inertialsense/IS-hdw/Products/IK-1/IK-1-2/README.md

# IK-1

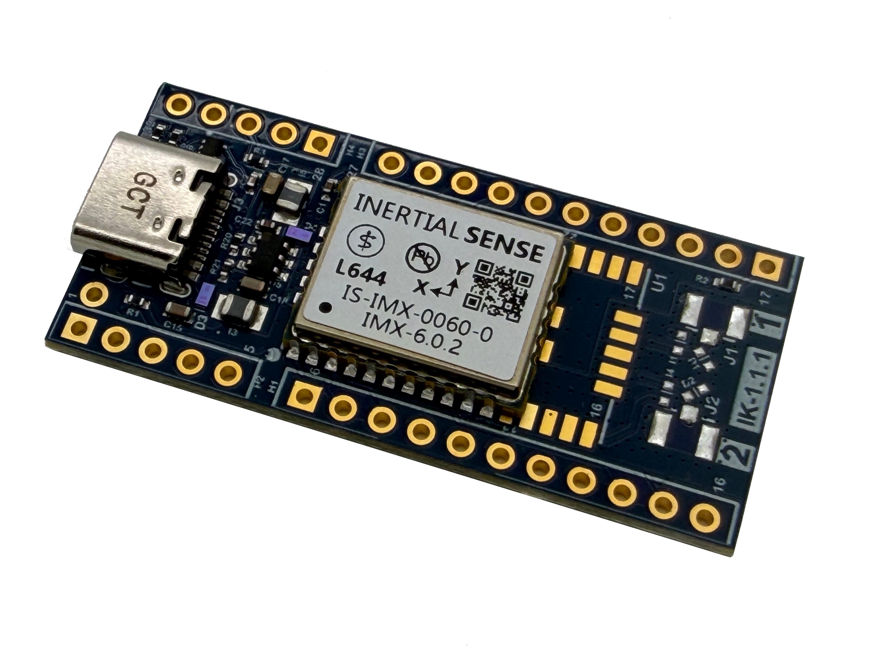
[picture p15: Products/IK-1/IK-1-2/Images/ik-1.png]
IK-1


The InertialSense IK-1 is a breakout board usable with the IMX or GPX dual multi-band GNSS receiver, exposing all pins for evaluation and development.  The IK-1 headers are 0.1" pitch.

## LICENSE



Use these Hardware Design files as you wish.  Inertial Sense is not liable for any claim, damages, or other liability resulting from their use.  See the included *LICENSE* file for details.

------

## Support

Email - support@inertialsense.com

------

(c) 2014-2026 Inertial Sense, Inc.
