inertialsense/IS-hdw/Products/EVB-1/EVB-1-5/Images/evb-1.5.png

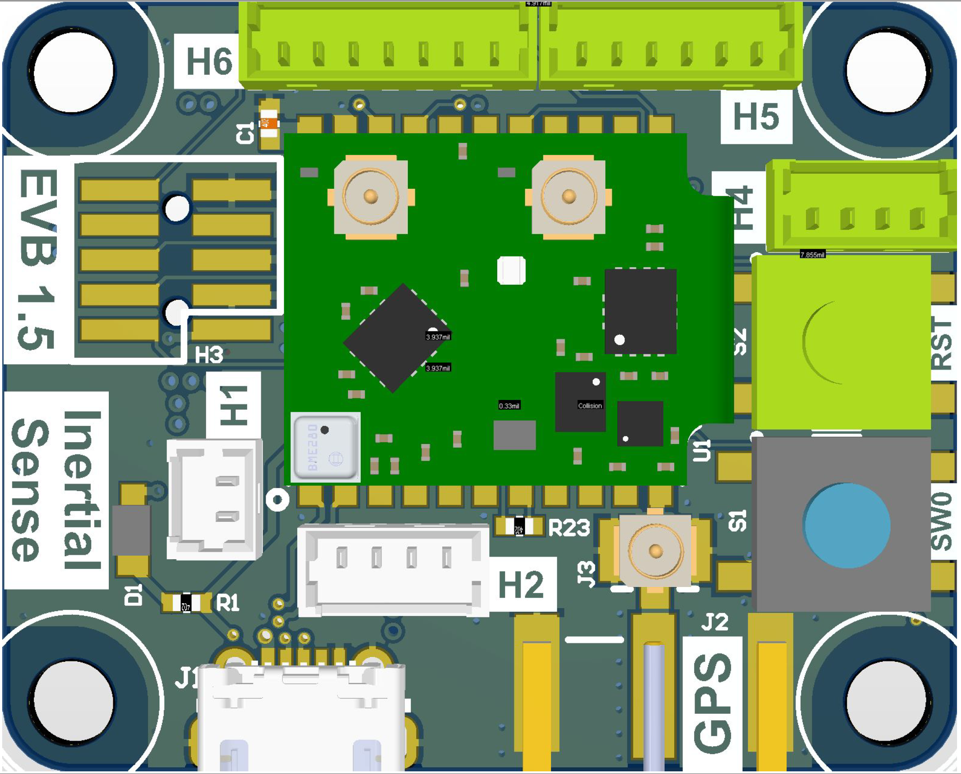
Products/EVB-1/EVB-1-5/Images/evb-1.5.png
