inertialsense/IS-hdw/Products/EVB-2/EVB-2-1/Images/bottom.png

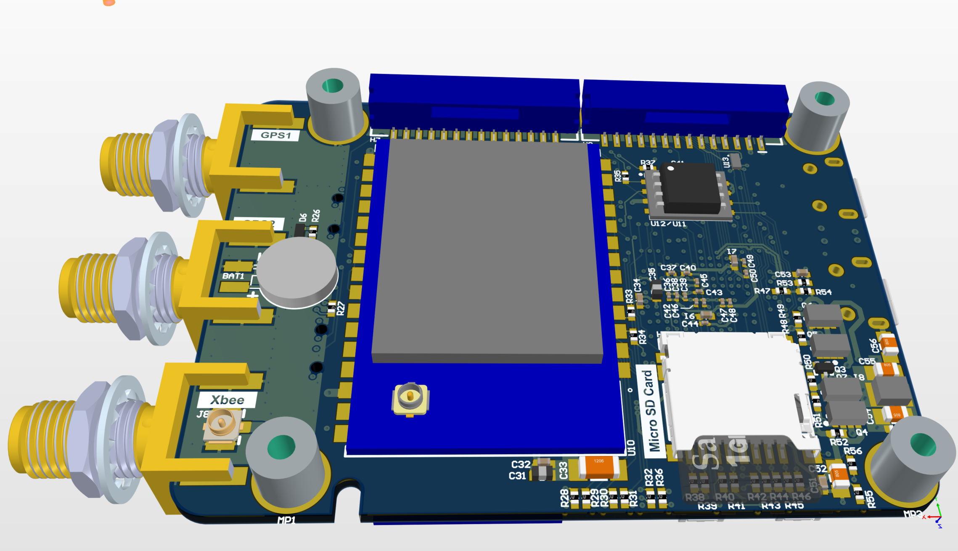
Products/EVB-2/EVB-2-1/Images/bottom.png
