inertialsense/IS-hdw/Products/EVB-2/EVB-2-1/Images/evb-2.1.2.png

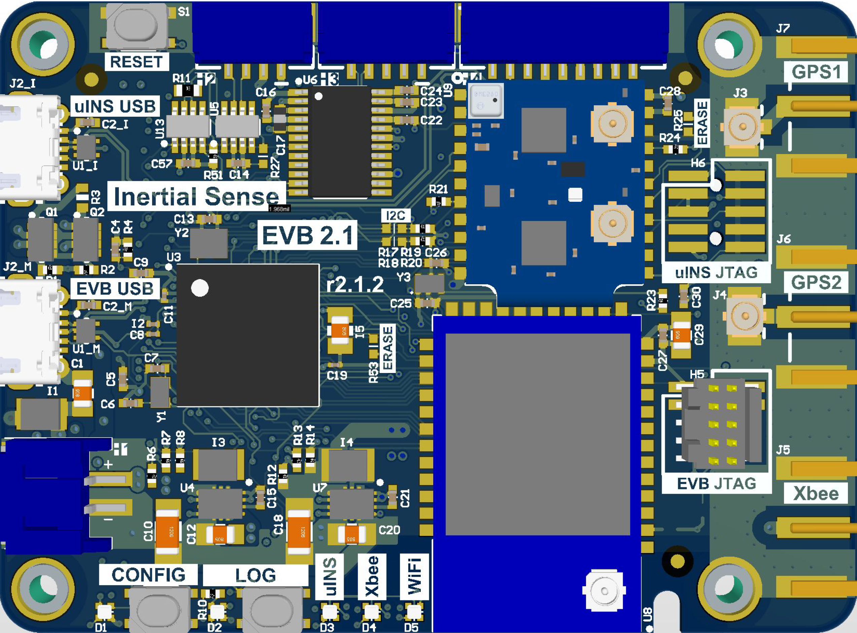
Products/EVB-2/EVB-2-1/Images/evb-2.1.2.png
