inertialsense/IS-hdw/Products/EVB-2/EVB-2-1/Images/iso-sd.jpg

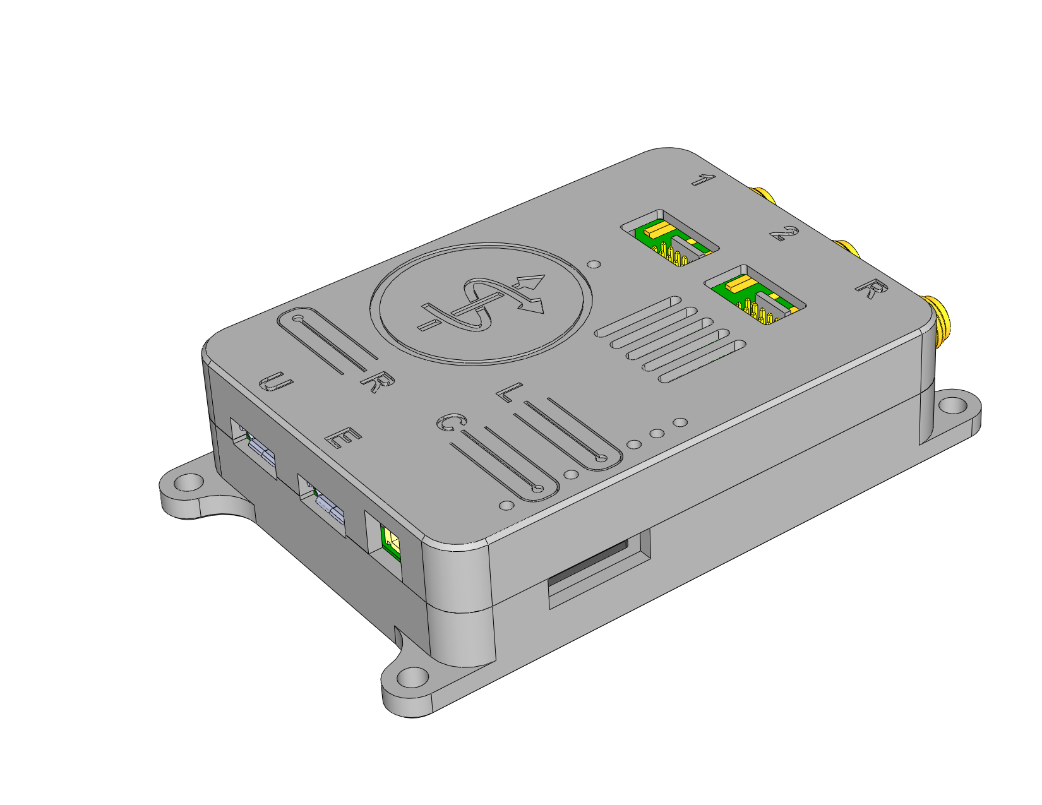
Products/EVB-2/EVB-2-1/Images/iso-sd.jpg
