inertialsense/IS-hdw/Products/GPX-1/GPX-1-0/Images/GPX_1.0.1_top.png

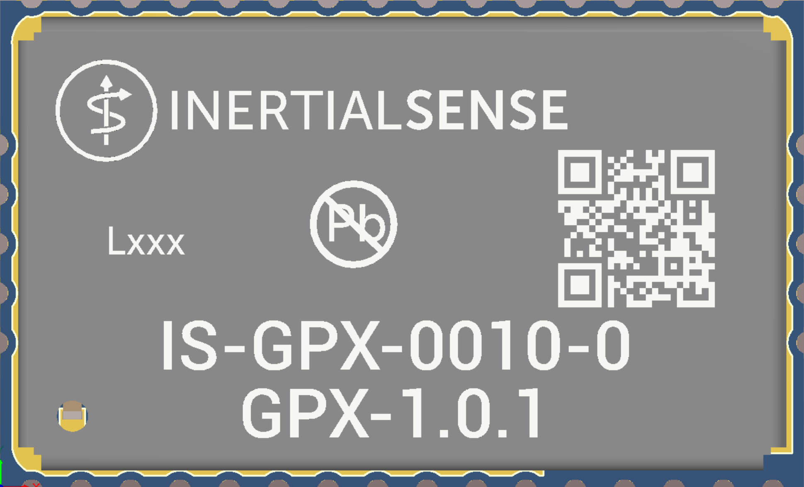
Products/GPX-1/GPX-1-0/Images/GPX_1.0.1_top.png
