inertialsense/IS-hdw/Products/IG-1/IG-1-2-G2/3D_Model/IG-1.2-G2.png

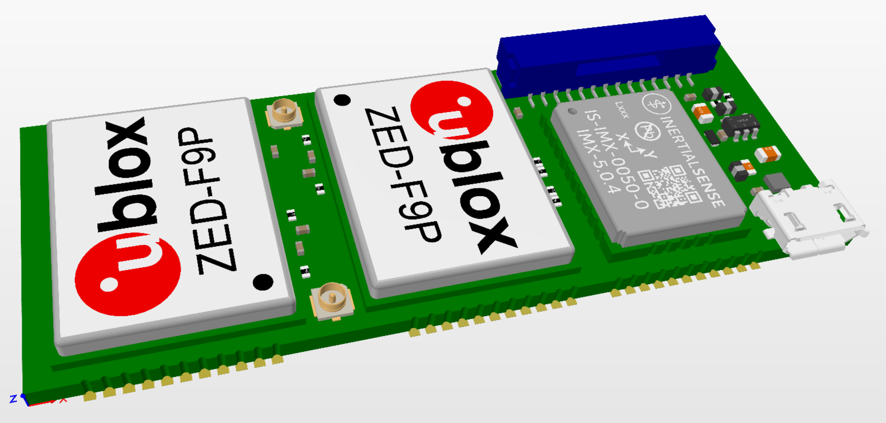
Products/IG-1/IG-1-2-G2/3D_Model/IG-1.2-G2.png
