inertialsense/IS-hdw/Products/IG-1/IG-1-2-G2/Images/IG-1.1_iso.png

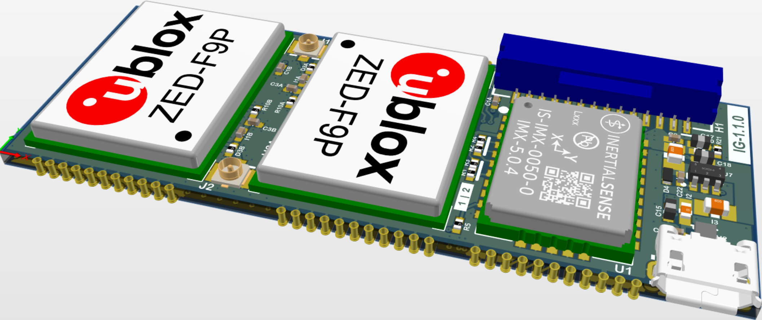
Products/IG-1/IG-1-2-G2/Images/IG-1.1_iso.png
