inertialsense/IS-hdw/Products/IG-3/IG-3-0-G/3D_Model/ig-2.1_1000w.png

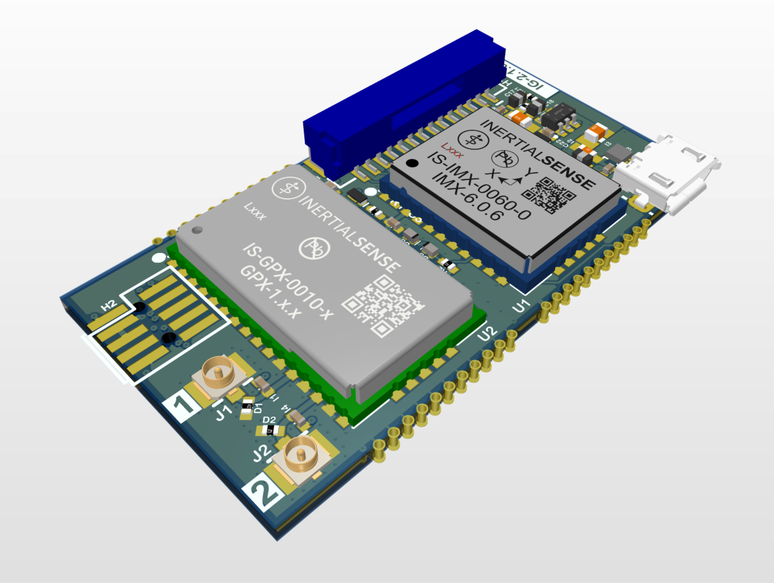
Products/IG-3/IG-3-0-G/3D_Model/ig-2.1_1000w.png
