inertialsense/IS-hdw/Products/IK-1/IK-1-1/Images/ik-1_cad.png

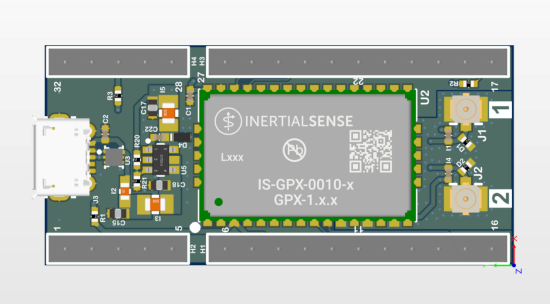
Products/IK-1/IK-1-1/Images/ik-1_cad.png
