inertialsense/IS-hdw/Products/IK-1/IK-1-2/Images/ik-1-gpx_cad.png

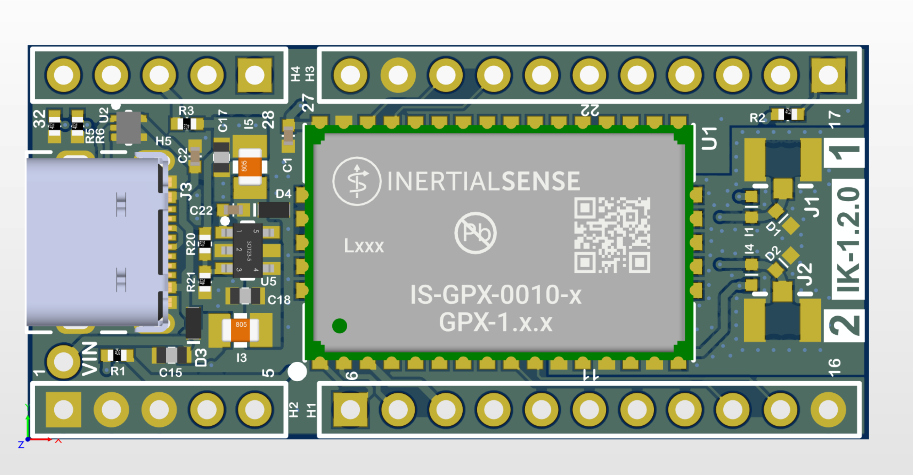
Products/IK-1/IK-1-2/Images/ik-1-gpx_cad.png
