inertialsense/IS-hdw/Products/IMX-5/IMX-5-0/3D_Model/IMX-5.0.4_top.png

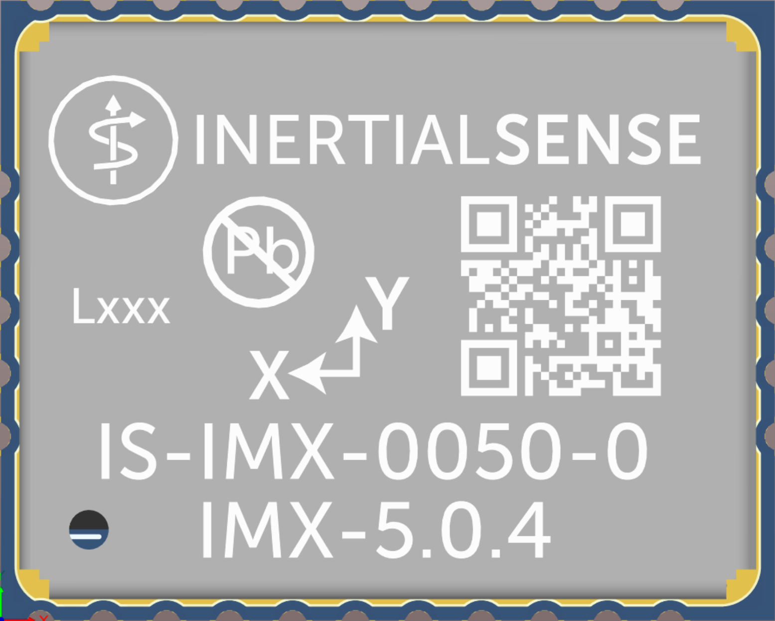
Products/IMX-5/IMX-5-0/3D_Model/IMX-5.0.4_top.png
