inertialsense/IS-hdw/Products/RUG-1/RUG-1-1/Images/rugged05x-600x400.png

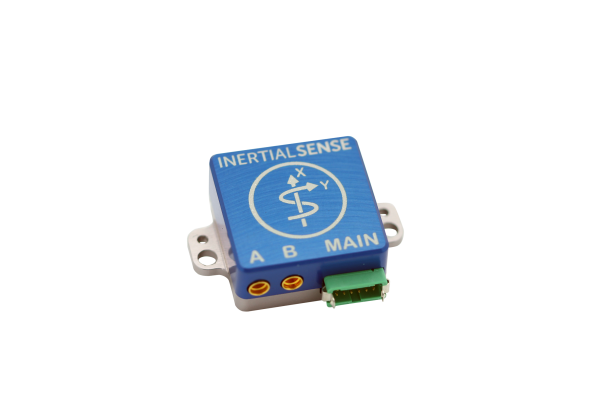
Products/RUG-1/RUG-1-1/Images/rugged05x-600x400.png
