inertialsense/IS-hdw/Products/RUG-1/RUG-1-1/Images/rugged 1 45d large.jpg

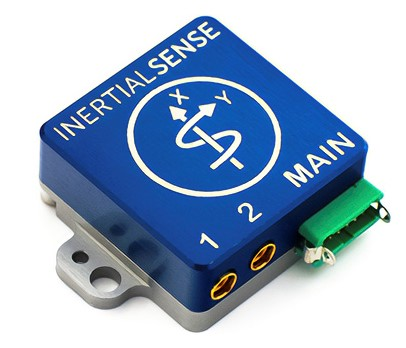
Products/RUG-1/RUG-1-1/Images/rugged 1 45d large.jpg
