inertialsense/IS-hdw/Products/RUG-2/RUG-2-0/Images/Rugged-Dip-Switch.jpg

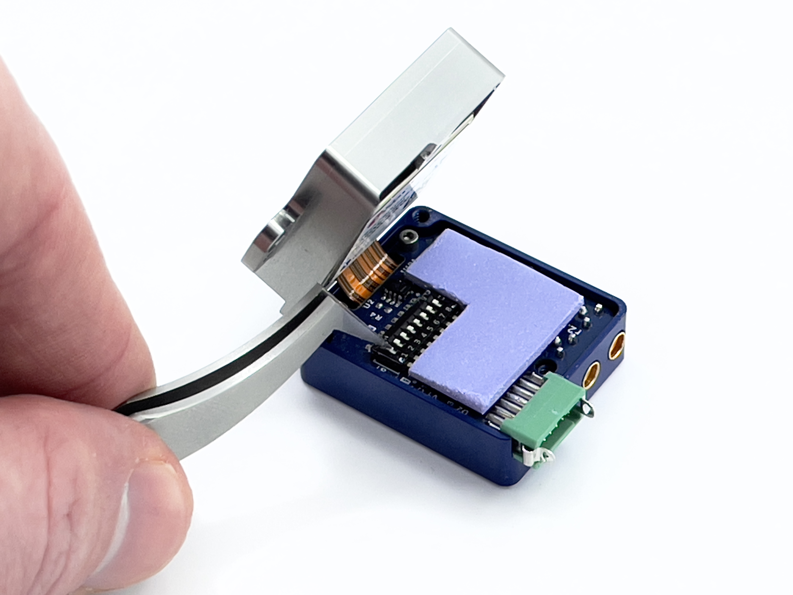
Products/RUG-2/RUG-2-0/Images/Rugged-Dip-Switch.jpg
