inertialsense/IS-hdw/Products/RUG-3/RUG-3-0-G0/Images/rug-3.0-G0_cad.png

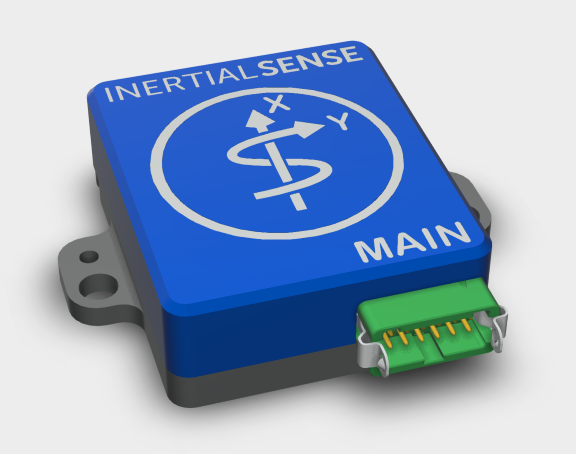
Products/RUG-3/RUG-3-0-G0/Images/rug-3.0-G0_cad.png
