inertialsense/IS-hdw/Products/EVB-2/EVB-2-1/Images/EVB-2 Case Assembly shaded con.jpg

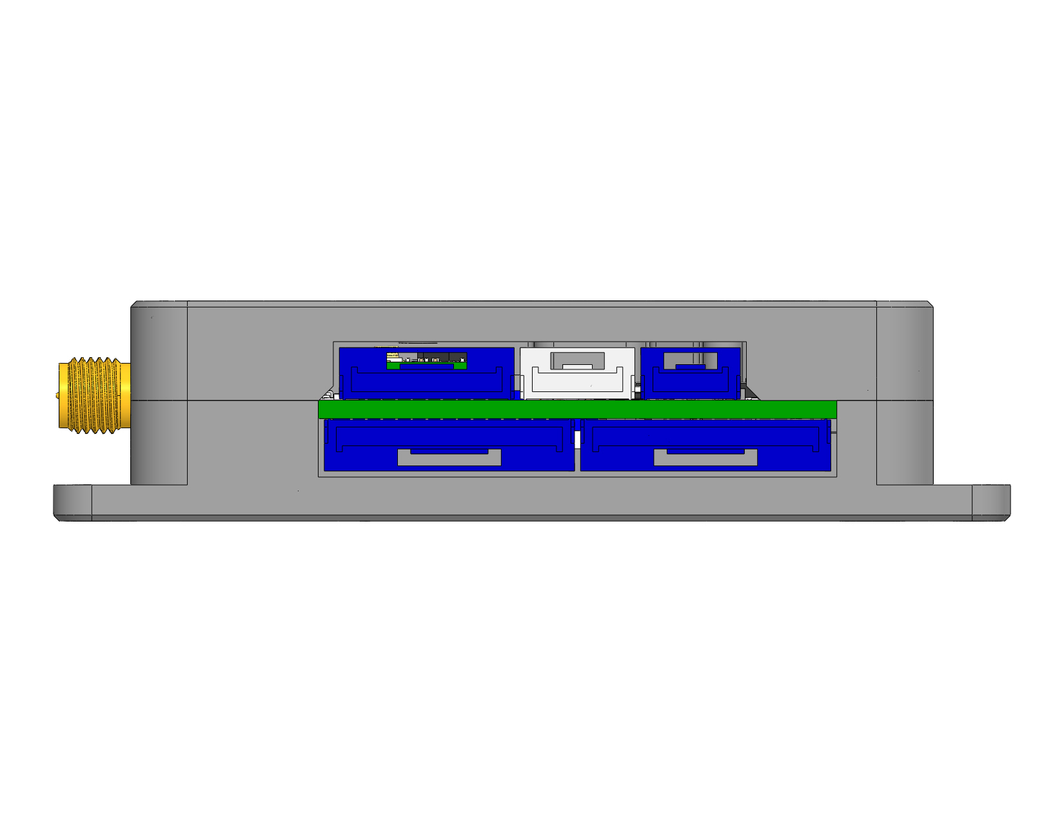
Products/EVB-2/EVB-2-1/Images/EVB-2 Case Assembly shaded con.jpg
