inertialsense/IS-hdw/Products/RUG-1/RUG-1-1/Images/comparison assembly shaded (7).jpg

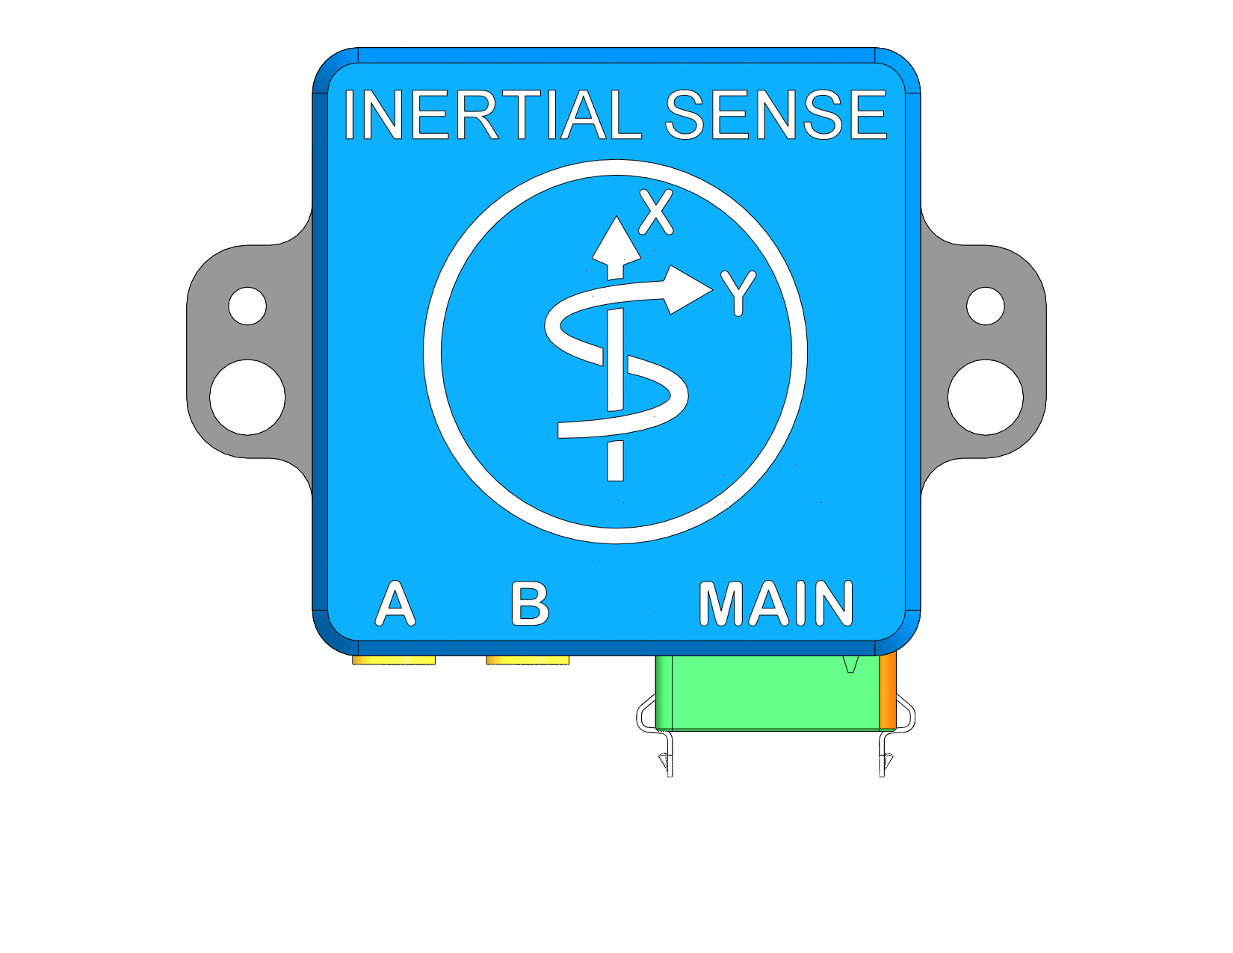
Products/RUG-1/RUG-1-1/Images/comparison assembly shaded (7).jpg
