inertialsense/IS-hdw/Products/RUG-1/RUG-1-1/Images/Ruggedized uINS Assembly shaded.jpg

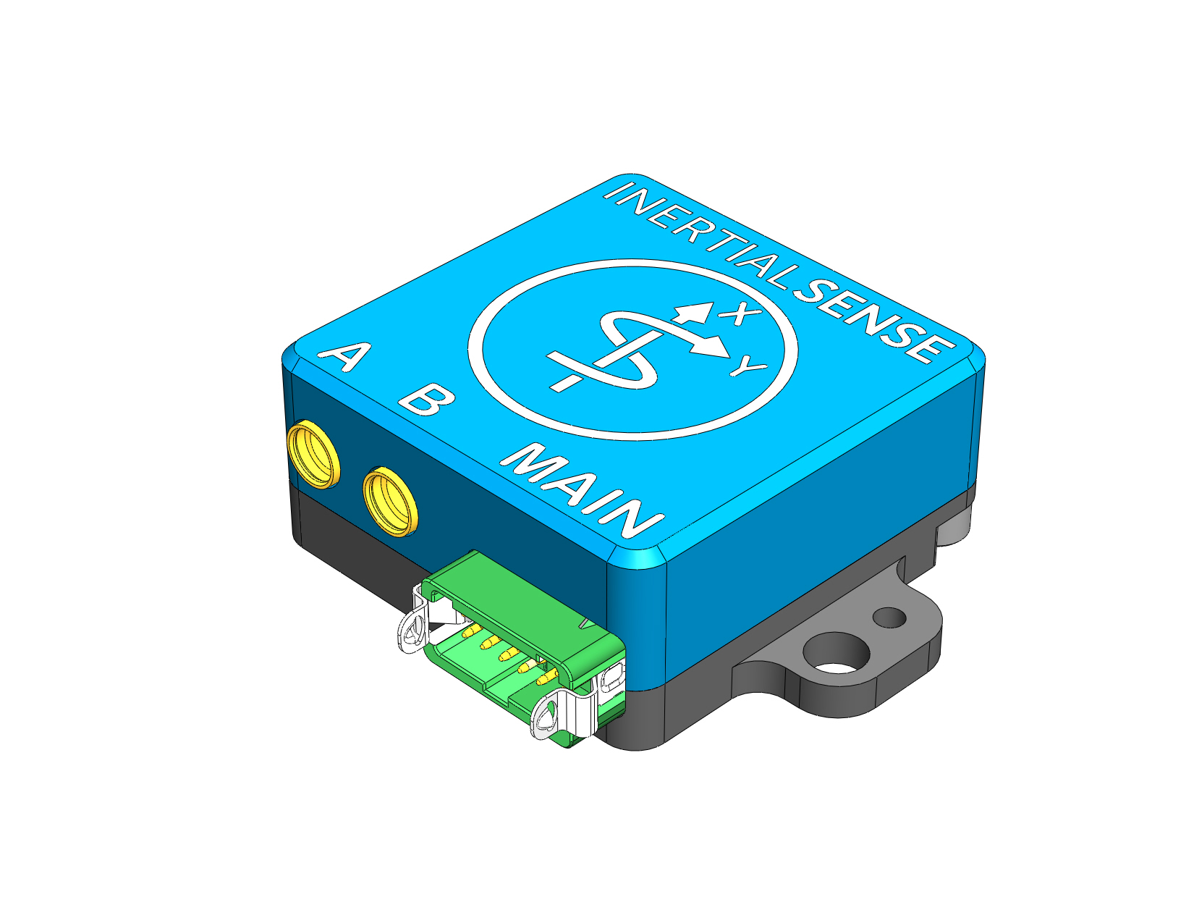
Products/RUG-1/RUG-1-1/Images/Ruggedized uINS Assembly shaded.jpg
