inertialsense/IS-hdw/Products/IG-2/IG-2-0/Schematic/IG-2_schematic.PDF

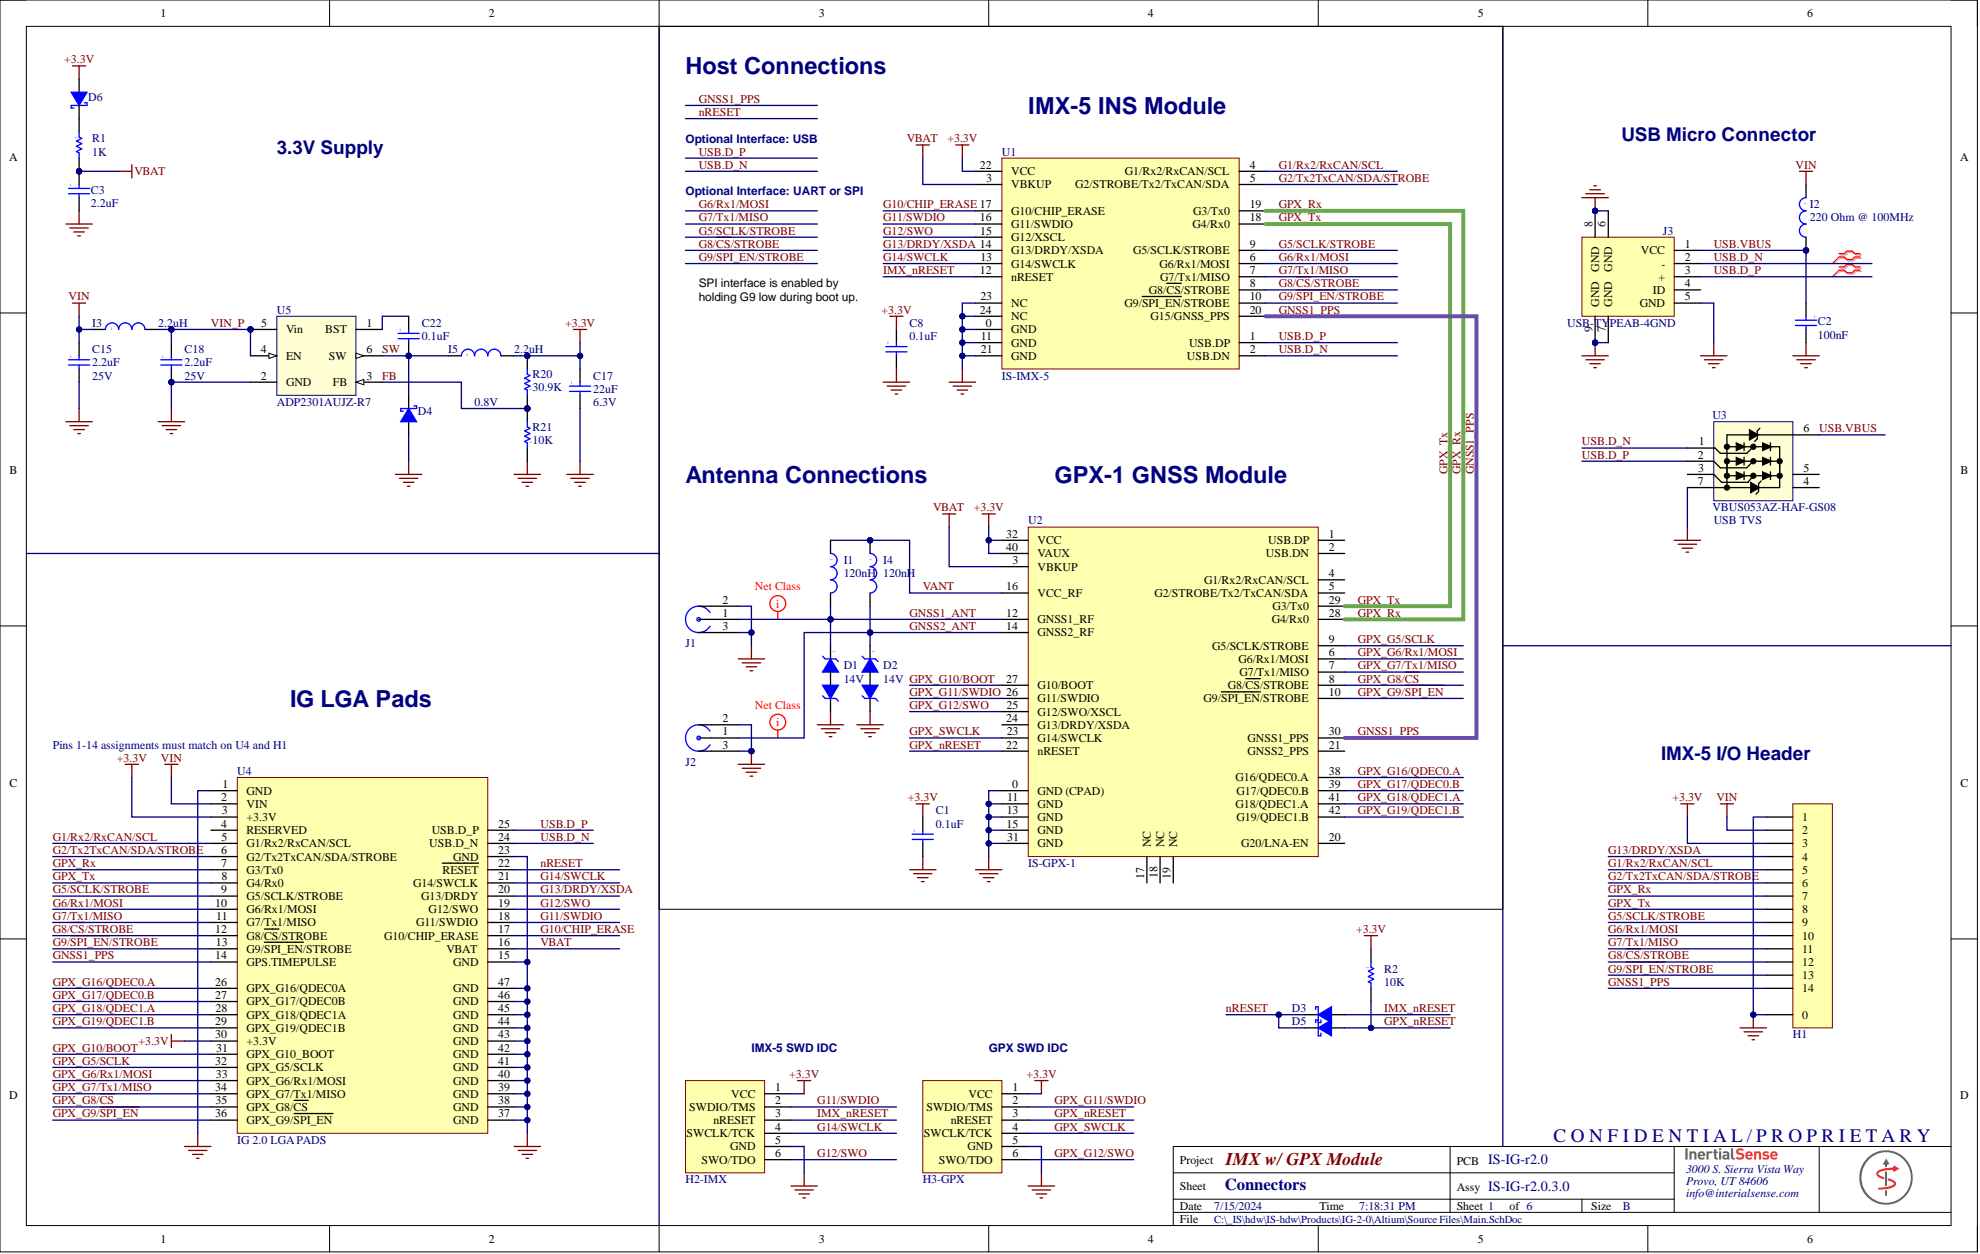
[picture p77: page 1]

G6/Rx1/MOSI G5/SCLK/STROBE G8/CS/STROBE G2/Tx2TxCAN/SDA/STROBE G1/Rx2/RxCAN/SCL

Optional Interface: UART or SPI
G5/SCLK/STROBE G8/CS/STROBE G9/SPI_EN/STROBE G6/Rx1/MOSI G7/Tx1/MISO

SPI interface is enabled by
holding G9 low during boot up.

1 1
GND 21

GPX_G6/Rx1/MOSI GPX_G7/Tx1/MISO GPX_G5/SCLK GPX_G8/CS GPX_G9/SPI_EN

Pins 1-14 assignments must match on U4 and H1

G6/Rx1/MOSI G5/SCLK/STROBE G8/CS/STROBE G2/Tx2TxCAN/SDA/STROBE G1/Rx2/RxCAN/SCL G9/SPI_EN/STROBE G7/Tx1/MISO GNSS1_PPS

G13/DRDY/XSDA

GPX_G10/BOOT
