inertialsense/IS-hdw/Products/EVB-2/EVB-2-1/Schematic/EVB-2-1-2_Schematic Prints.PDF

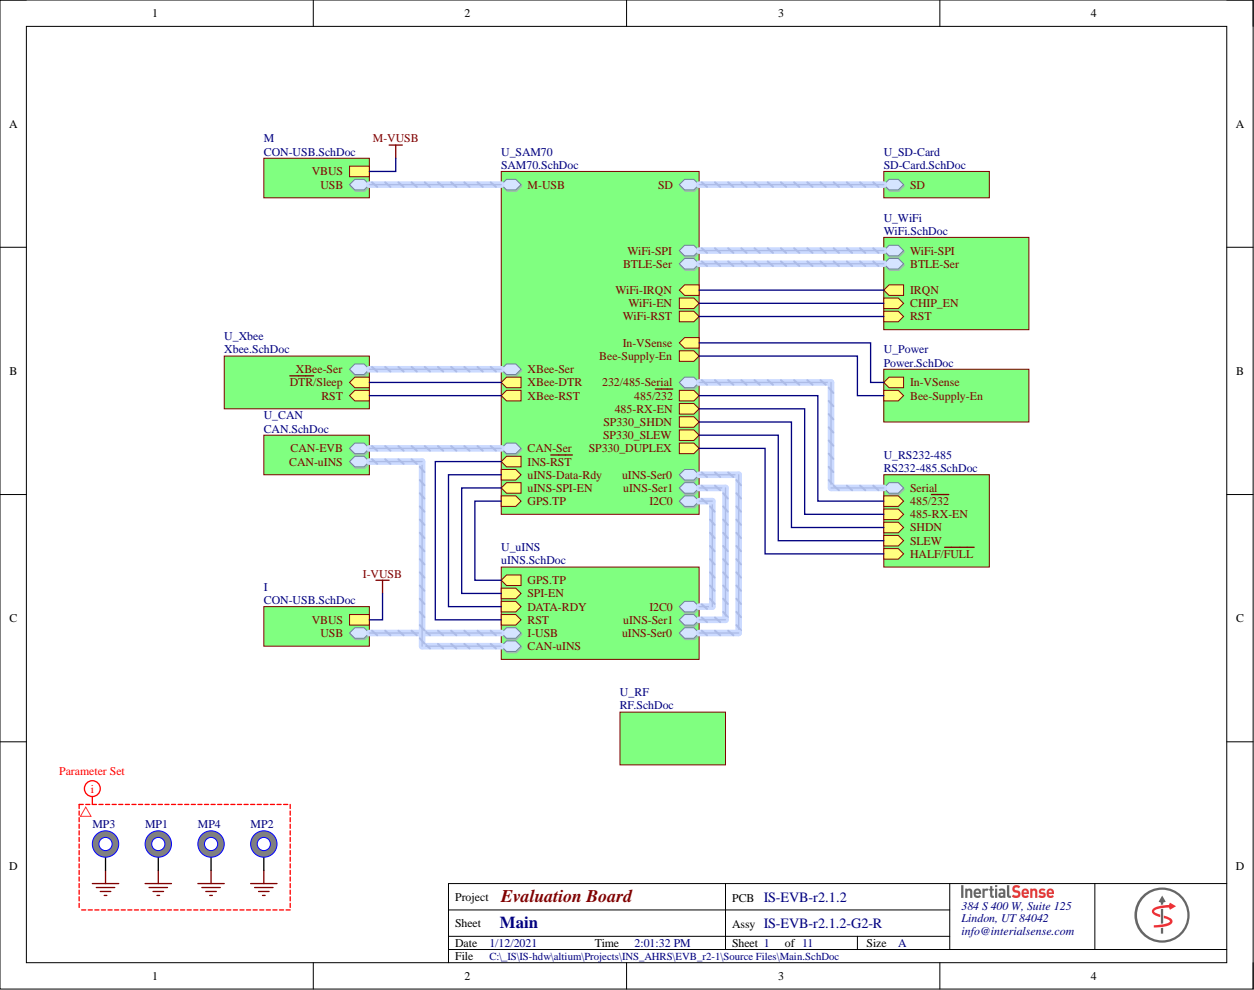
[picture p78: page 1]

U_SD-Card SD-Card.SchDoc

WiFi-IRQN WiFi-EN WiFi-RST

U_Power
Power.SchDoc
Bee-Supply-En In-VSense

IS-EVB-r2.1.2
PCB
IS-EVB-r2.1.2-
Assy
urce Files\Main.SchDo

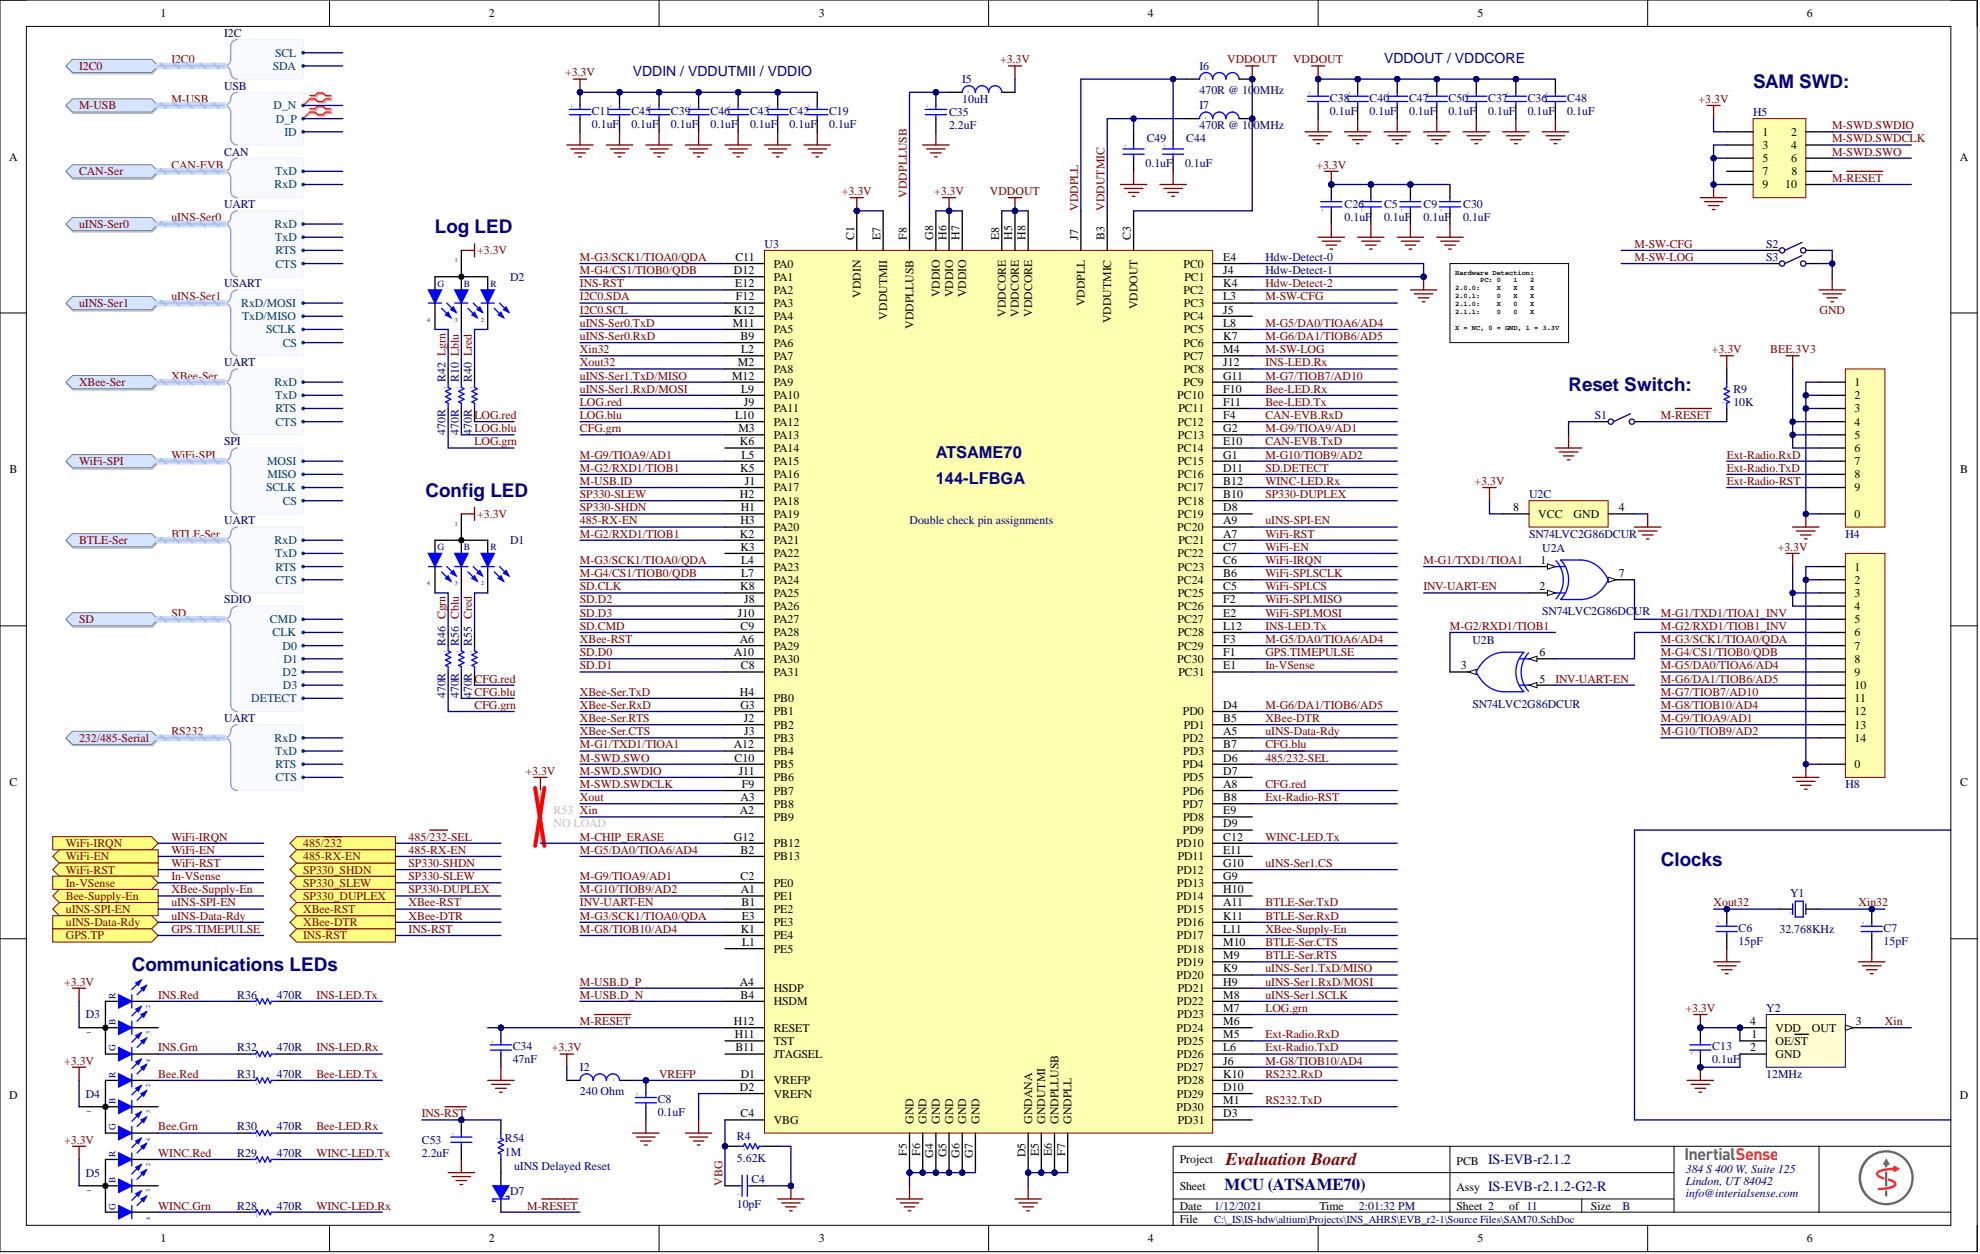
[picture p79: page 2]

GND F6 GND F5 Double check pin assignments

WiFi-RST
uINS-SPI-EN

C:\_IS\IS-hdw\altium\Projects\INS_AHRS\EVB_r2-1\Source Files\SAM70.SchDoc

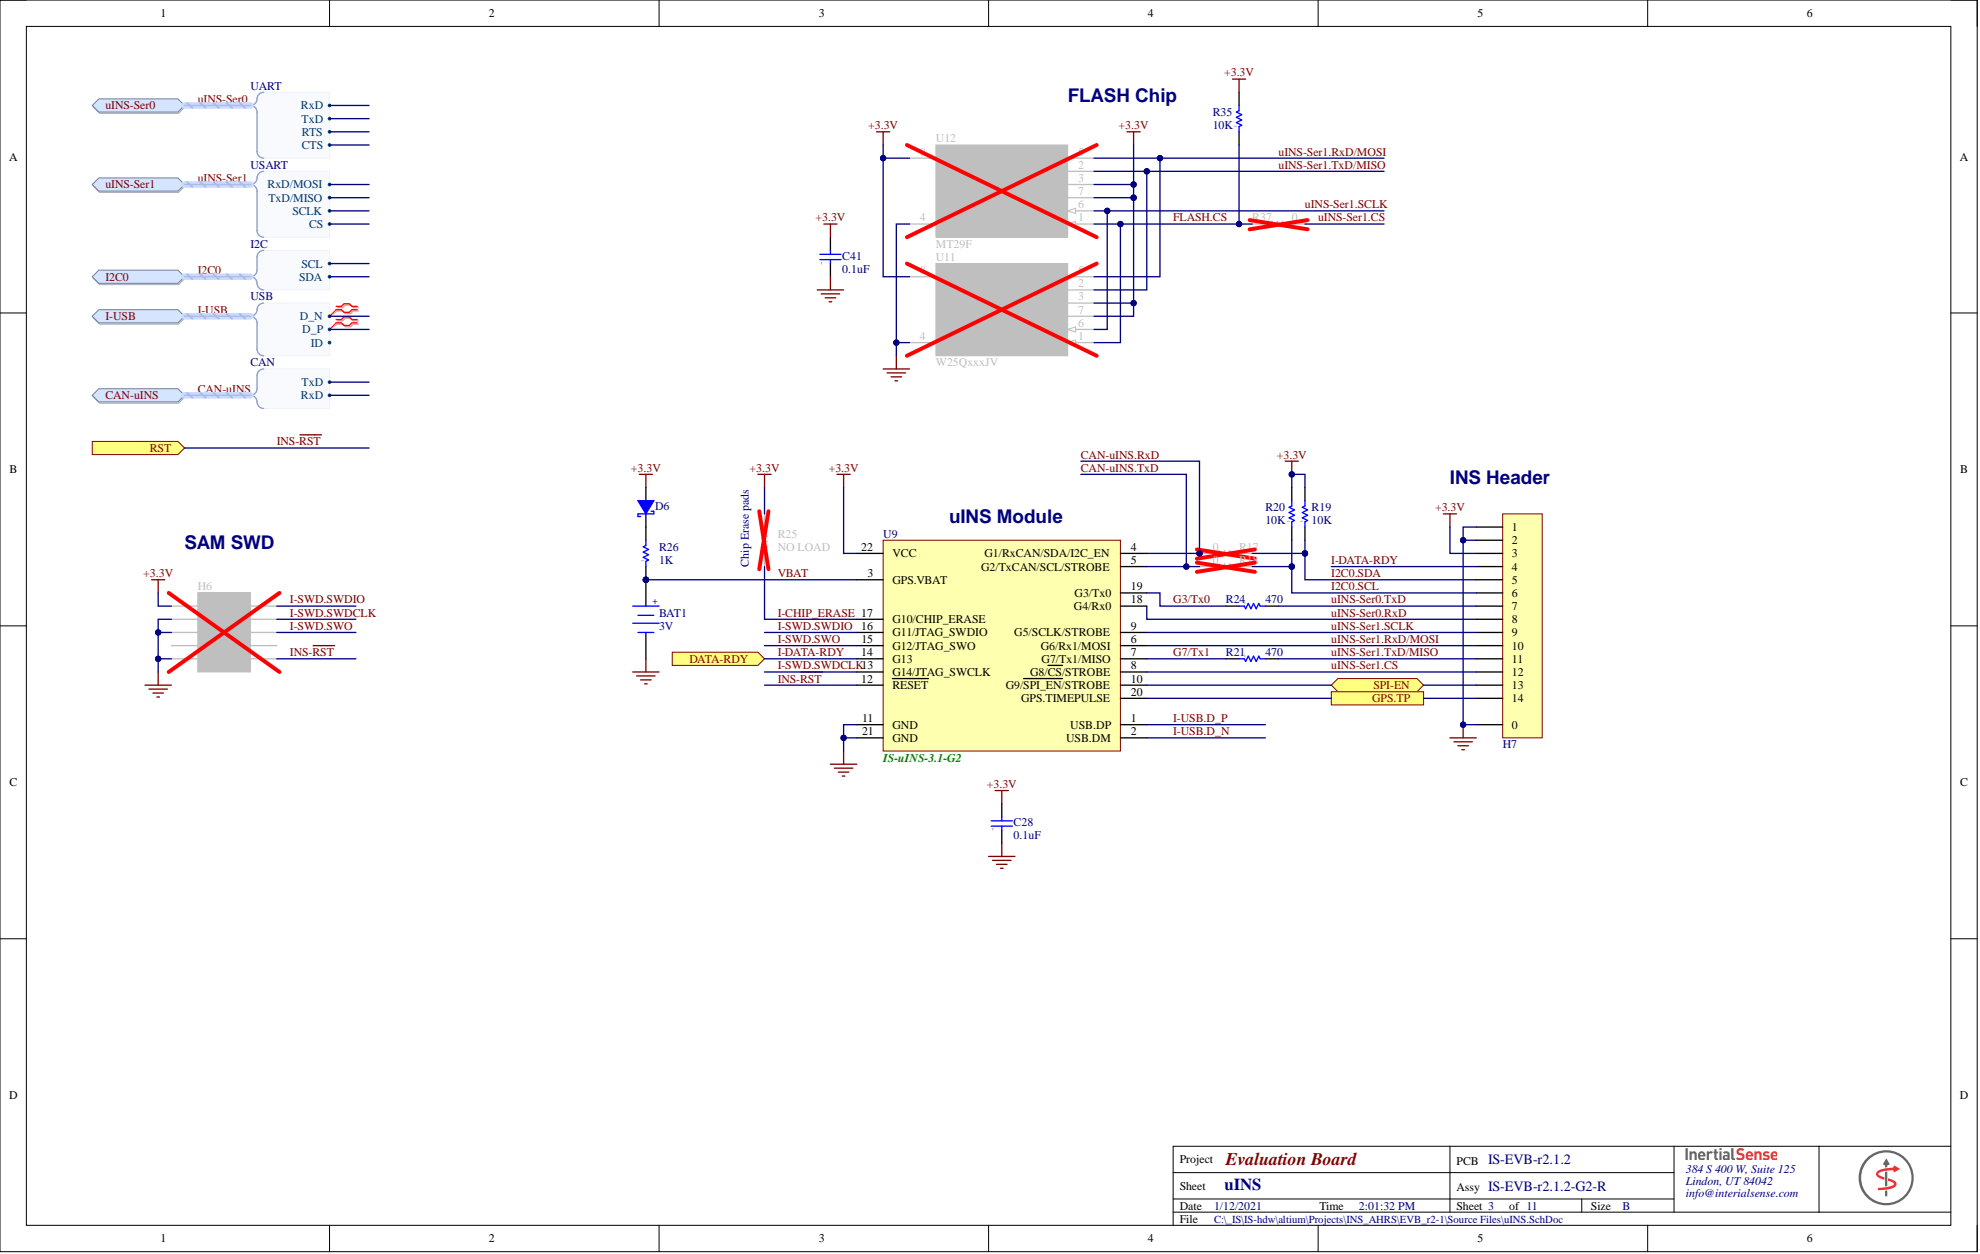
[picture p80: page 3]

C:\_IS\IS-hdw\altium\Projects\INS_AHRS\EVB_r2-1\Source Files\uINS.SchDoc

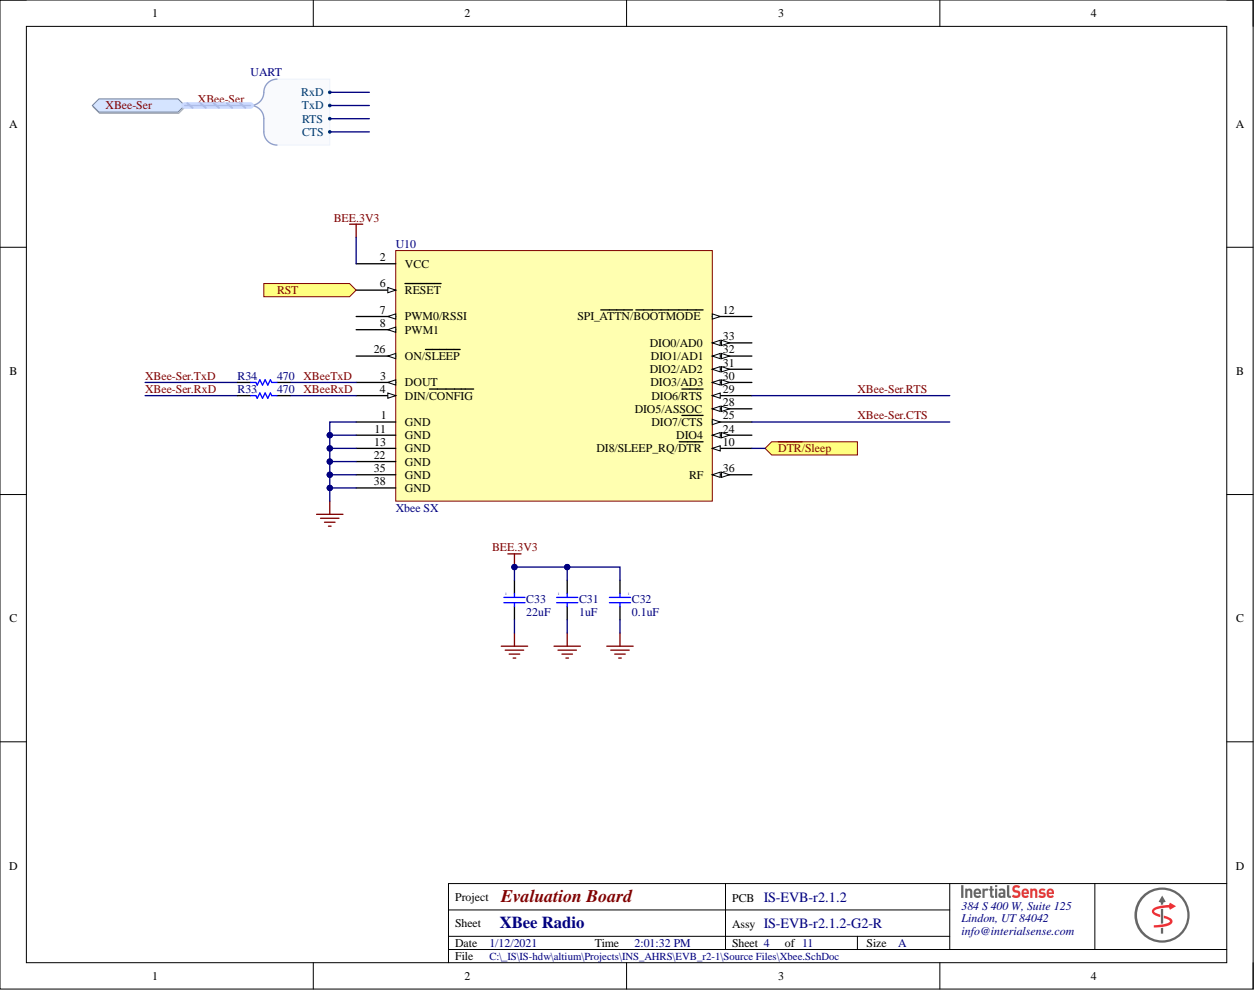
[picture p81: page 4]

C:\_IS\IS-hdw\altium\Projects\INS_AHRS\EVB_r2-1\Source Files\Xbee.SchDoc

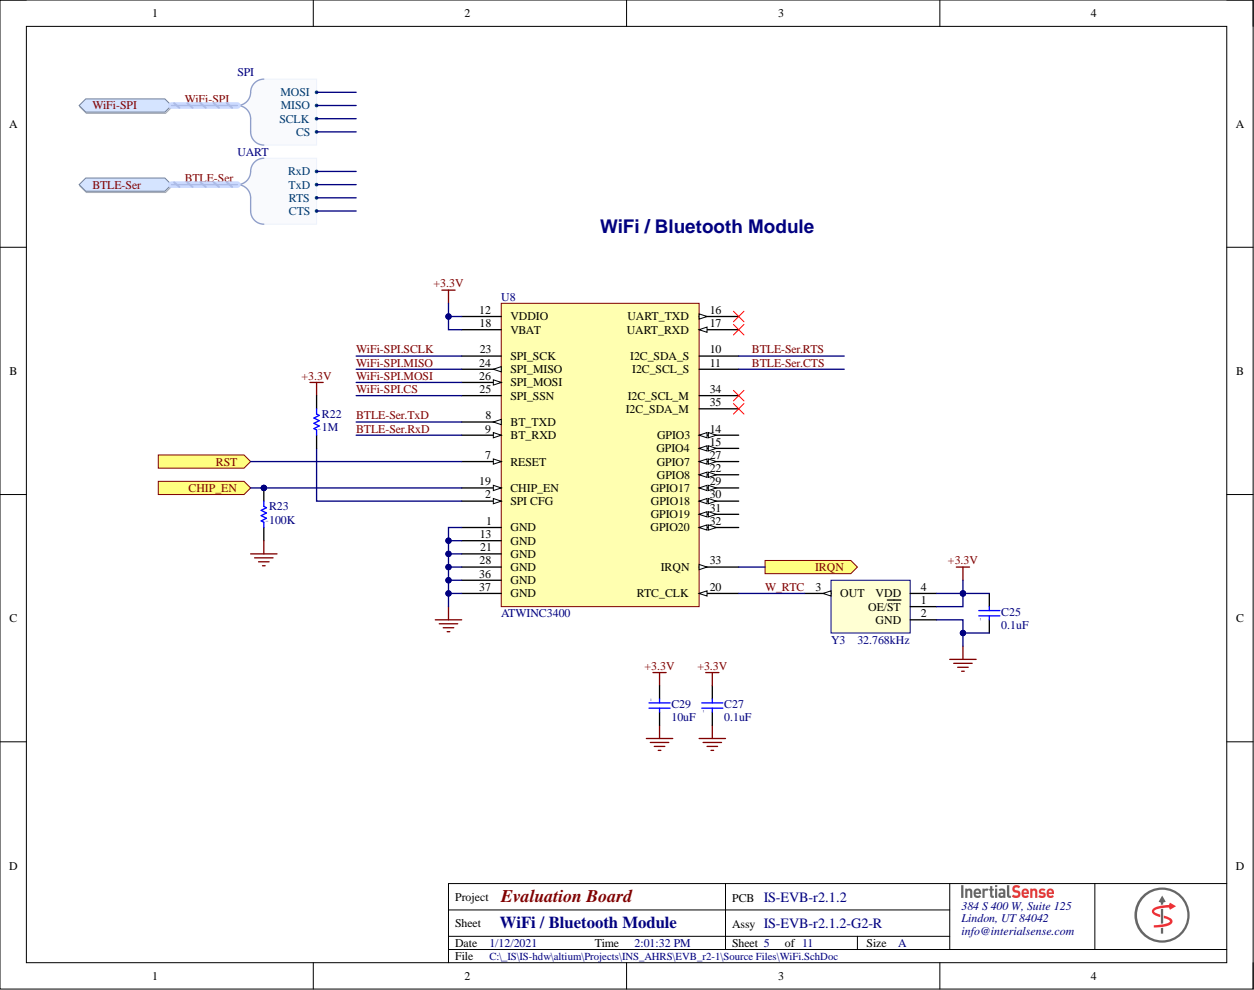
[picture p82: page 5]

C:\_IS\IS-hdw\altium\Projects\INS_AHRS\EVB_r2-1\Source Files\WiFi.SchDoc

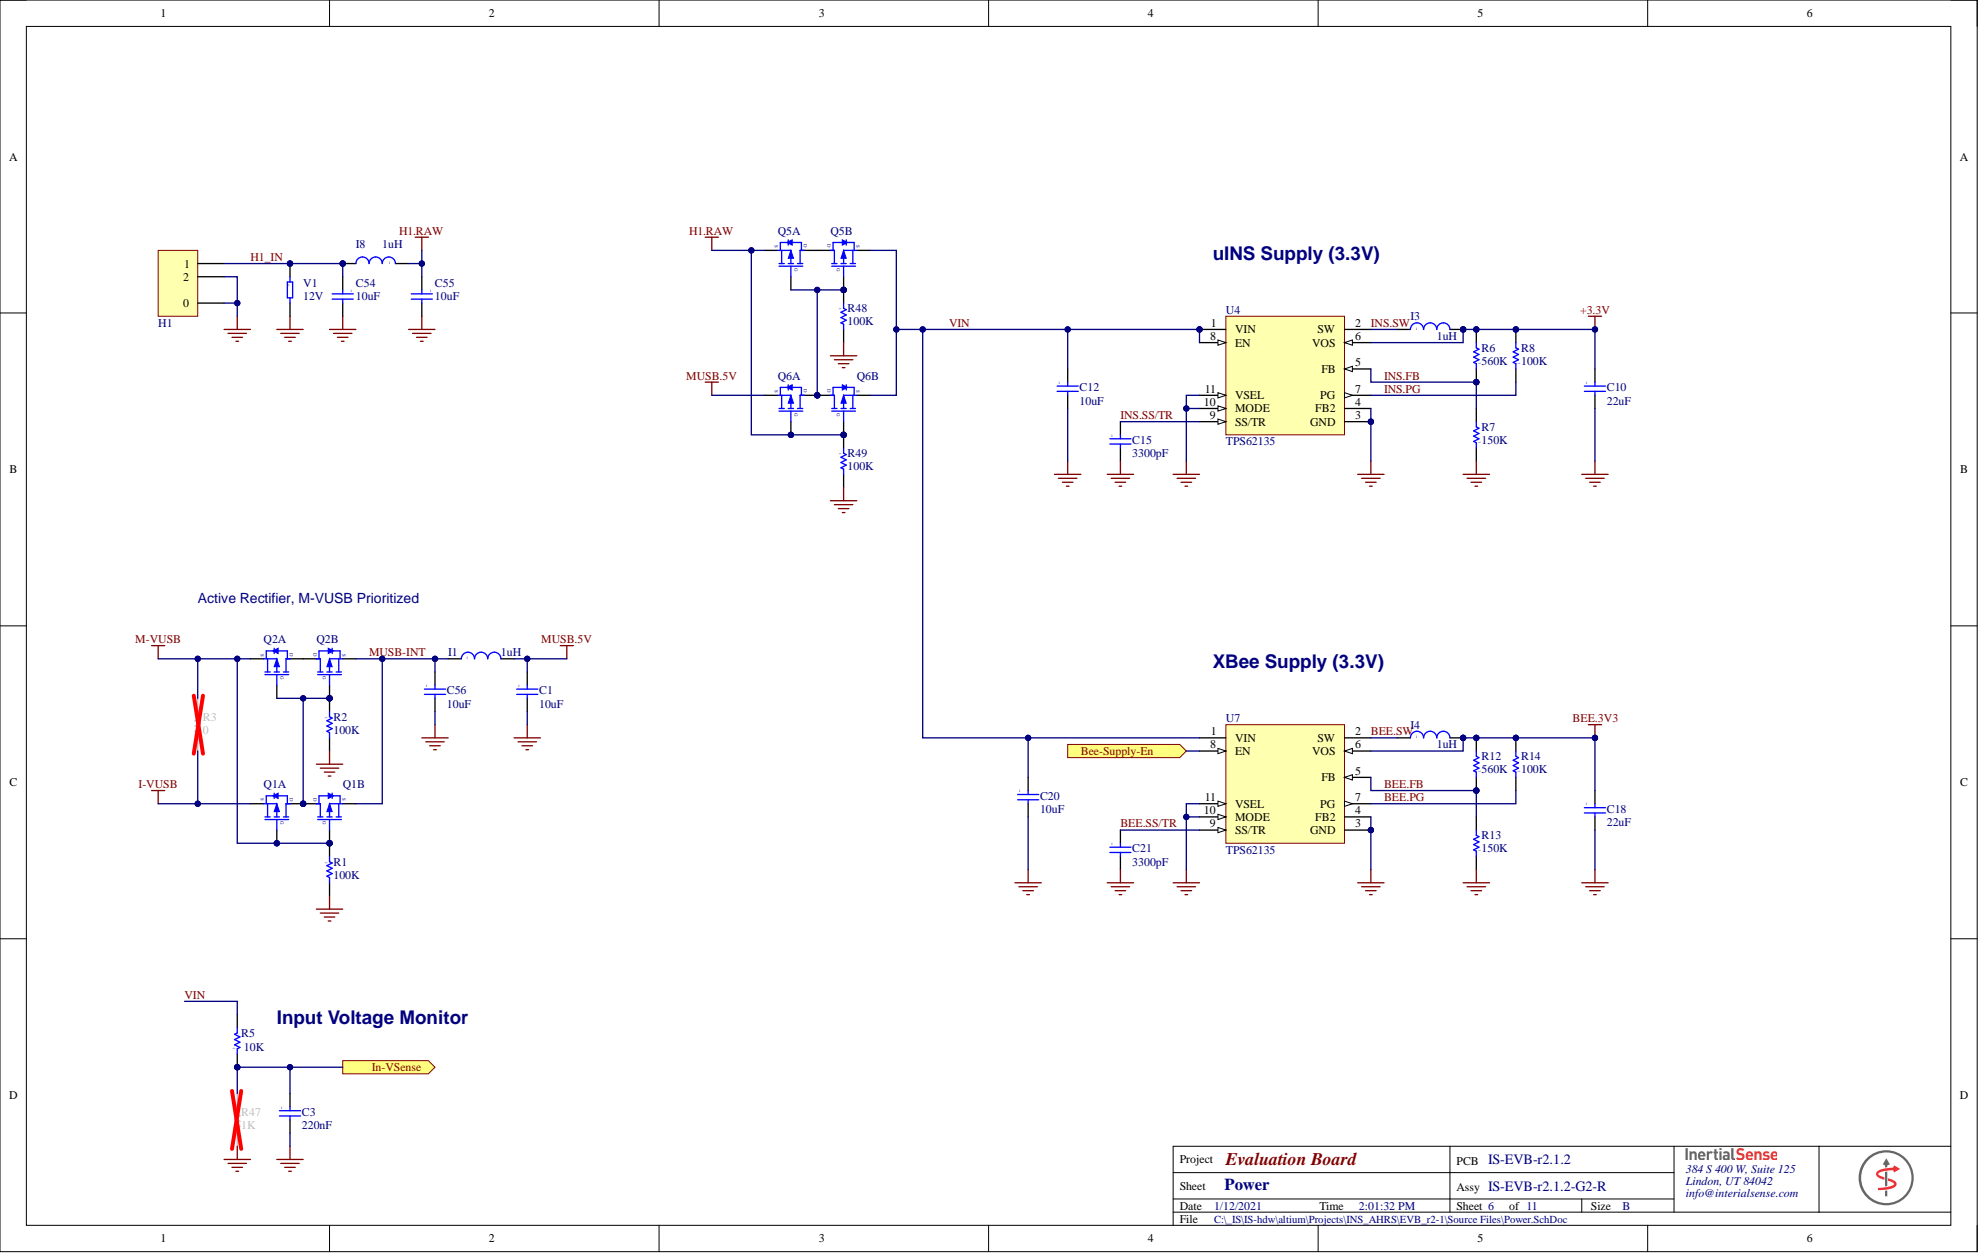
[picture p83: page 6]

Active Rectifier, M-VUSB Prioritized 10

urce Files\Power.SchDo

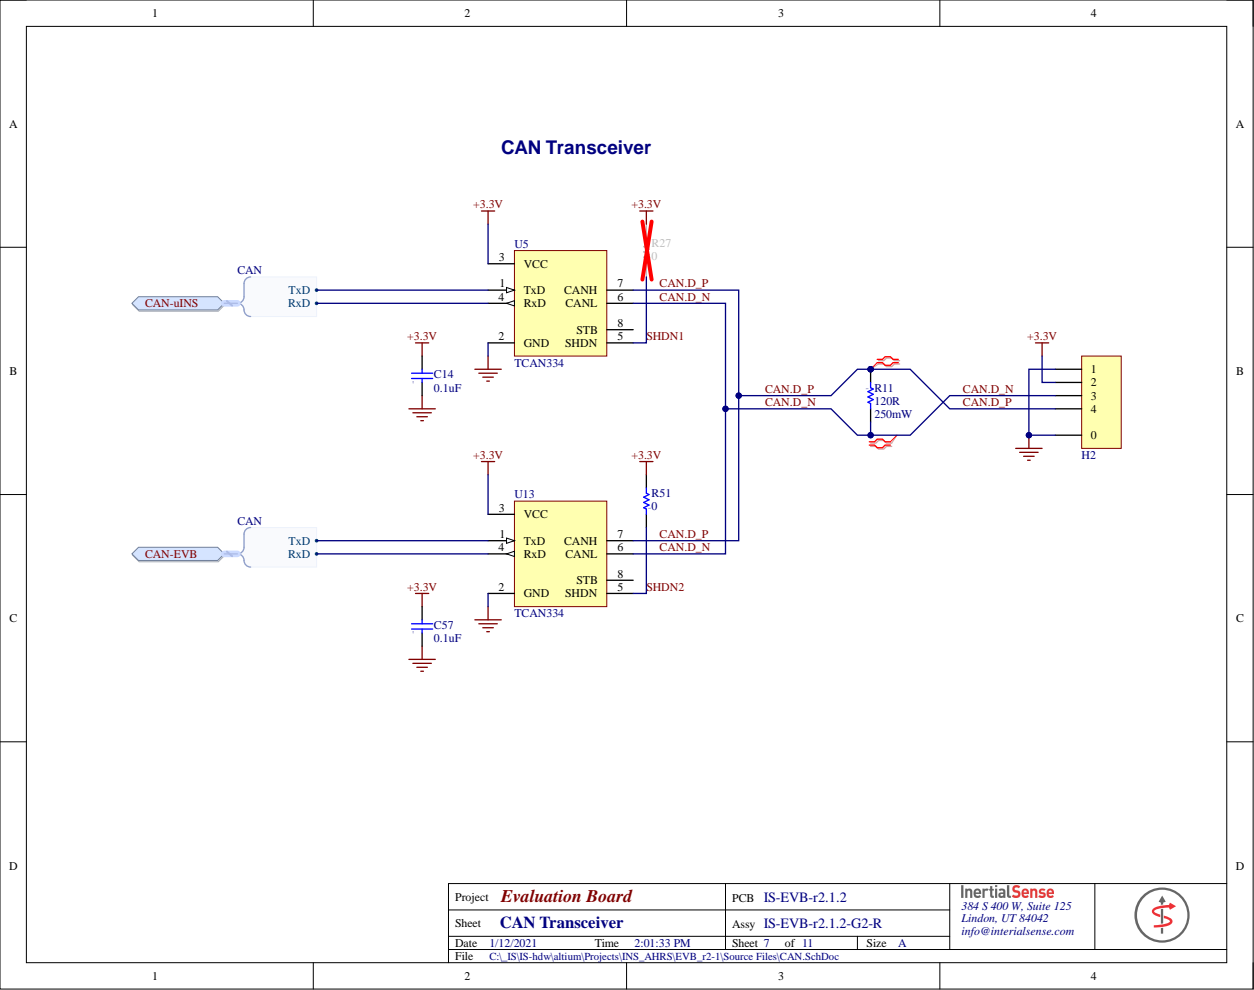
[picture p84: page 7]

urce Files\CAN.SchDo

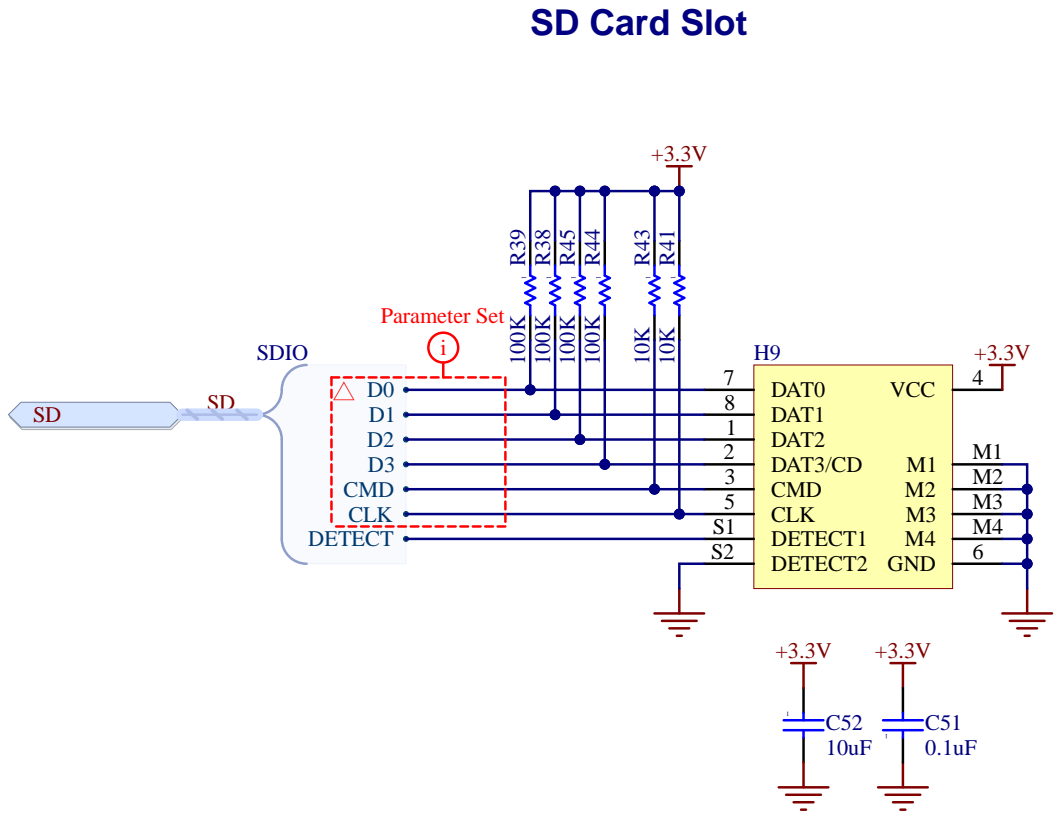
[picture p85: page 8]

C:\_IS\IS-hdw\altium\Projects\INS_AHRS\EVB_r2-1\Source Files\SD-Card.SchDoc

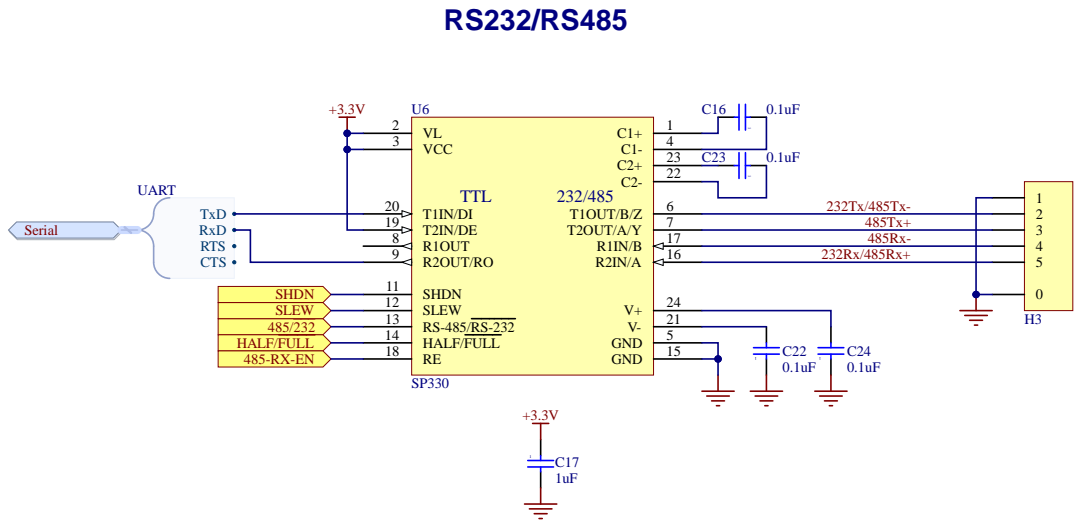
[picture p86: page 9]

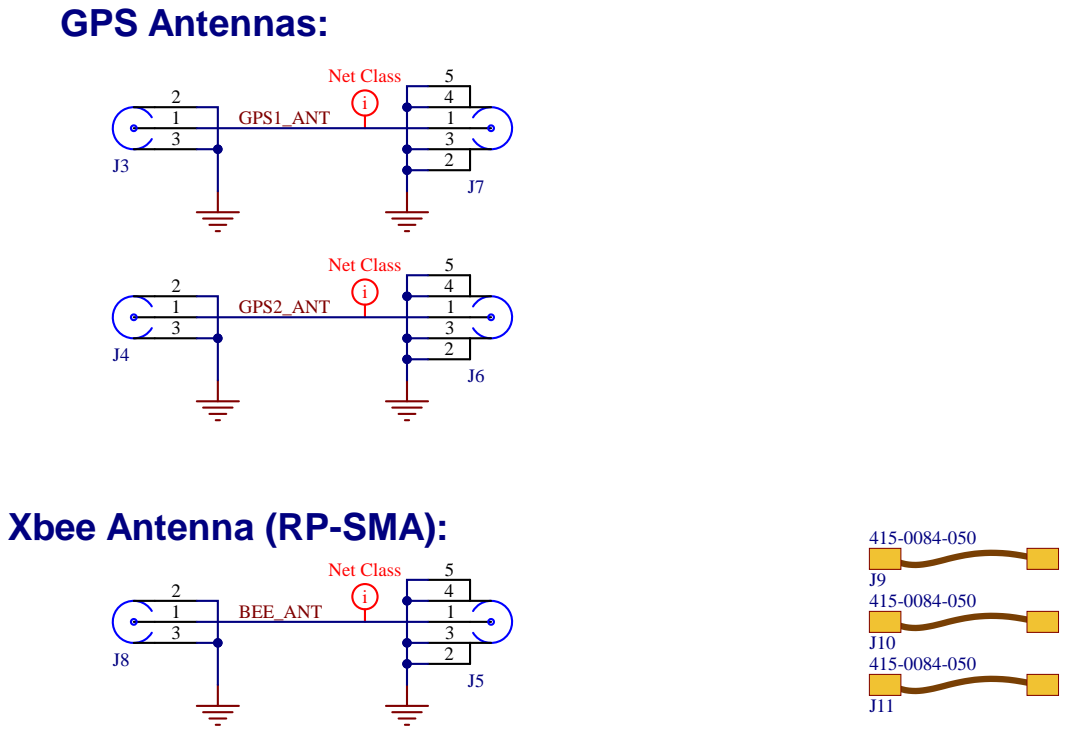
[picture p87: page 10]

Sheet 10 of
urce Files\RF.SchDo

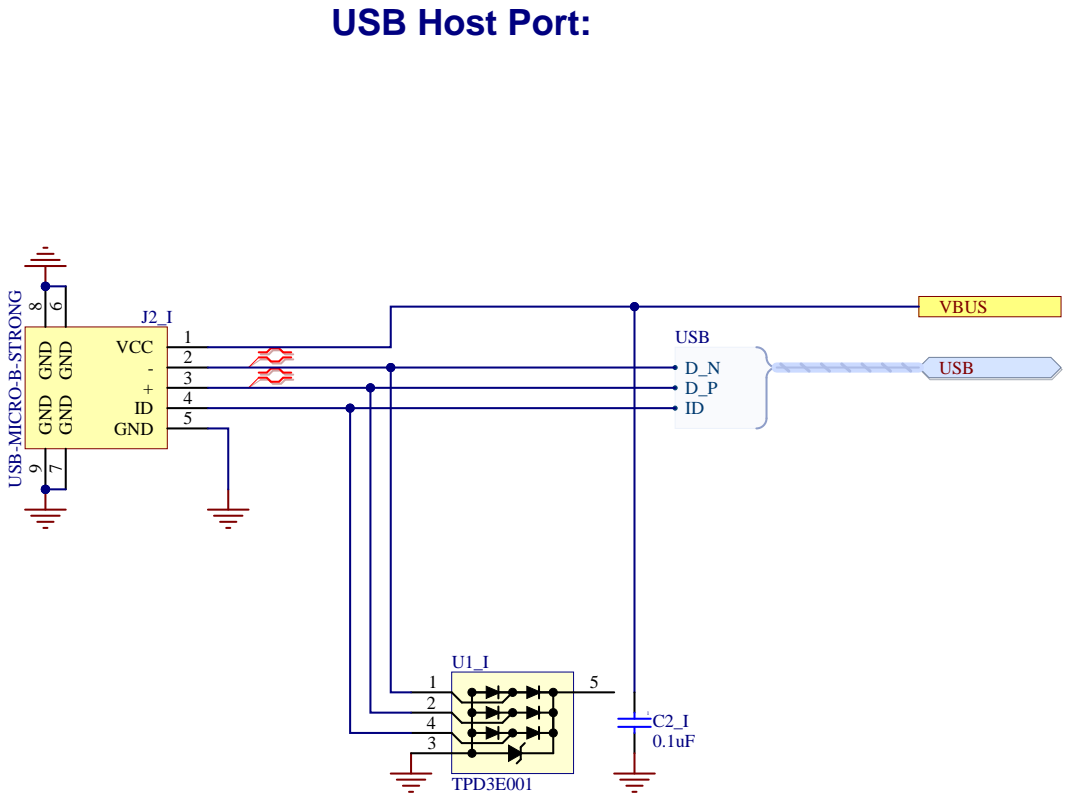
[picture p88: page 11]

urce Files\CON-USB.SchDo

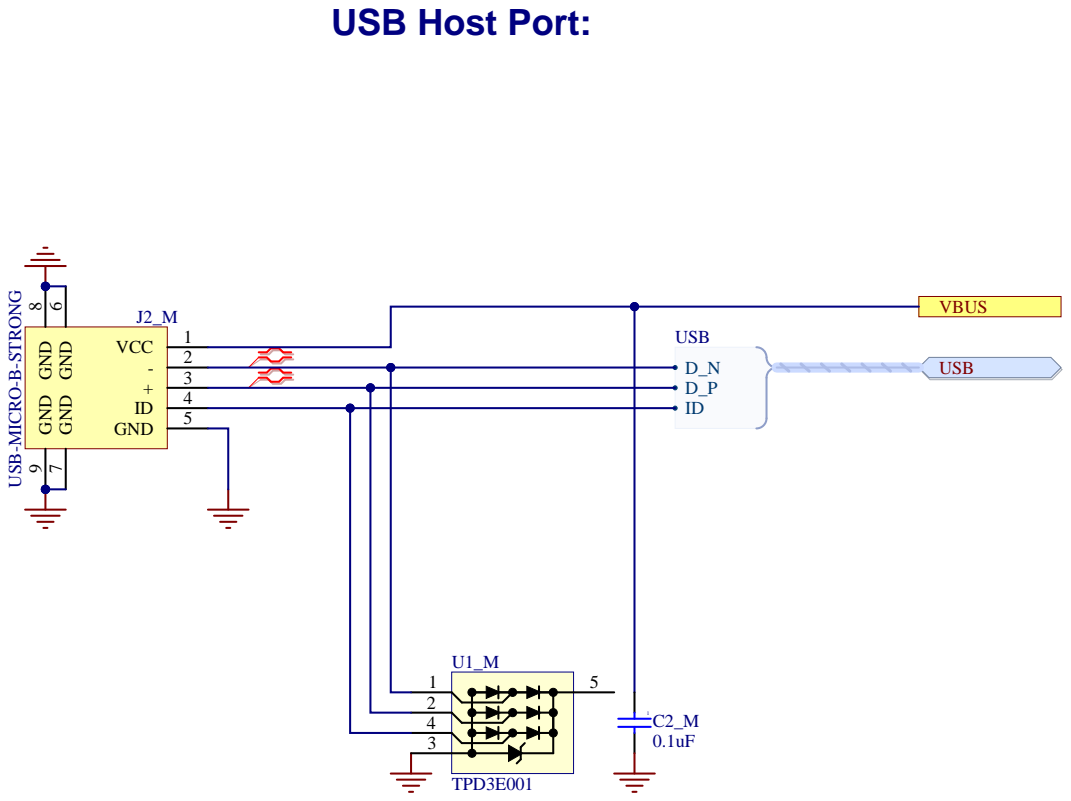
[picture p89: page 12]

urce Files\CON-USB.SchDo
