inertialsense/IS-hdw/Products/IG-1/IG-1-2-G2/Schematic/IG-1_schematic.PDF

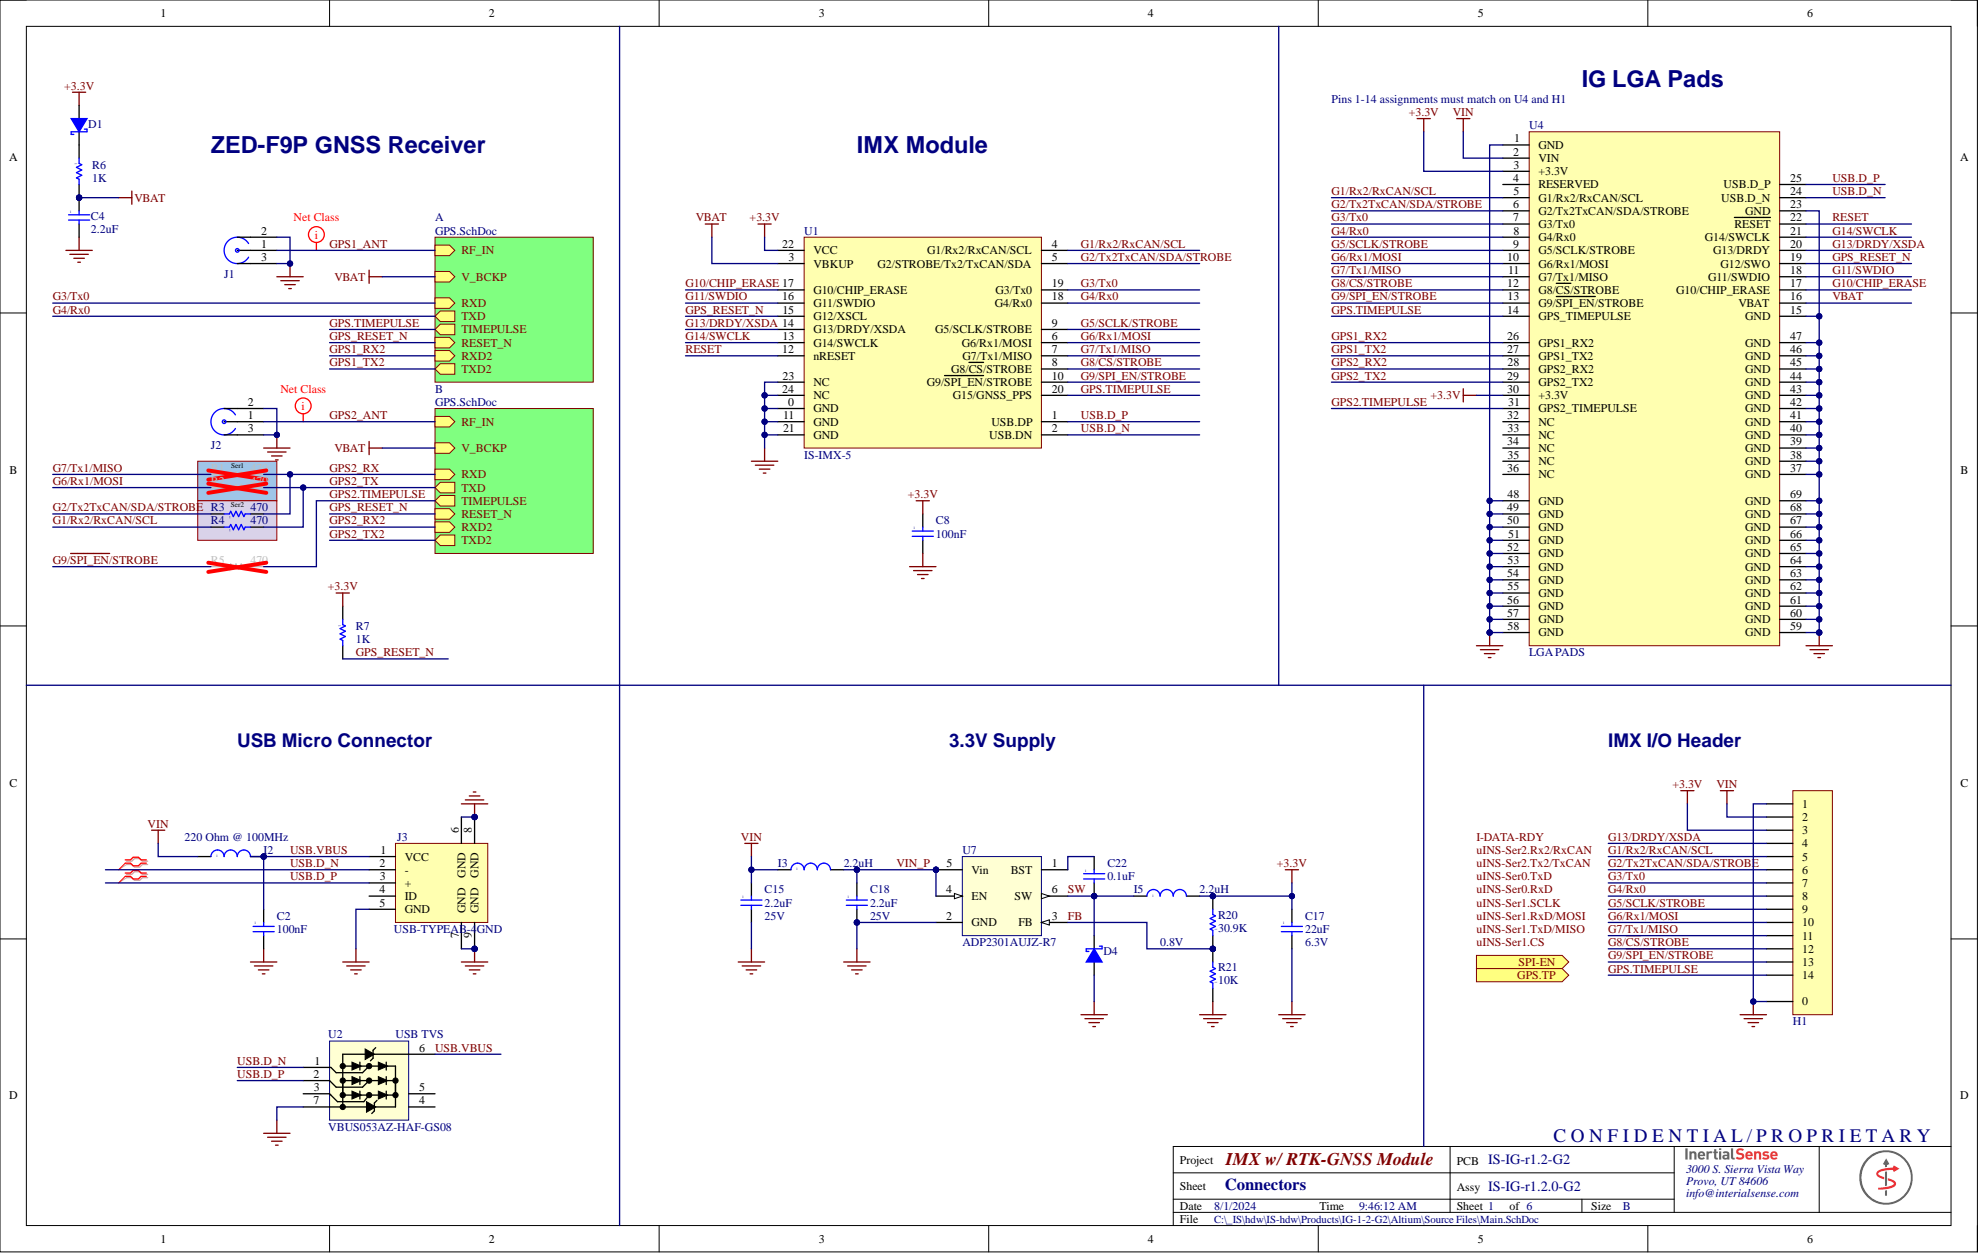
[picture p90: page 1]

Pins 1-14 assignments must match on U4 and H1

G6/Rx1/MOSI G5/SCLK/STROBE G8/CS/STROBE G2/Tx2TxCAN/SDA/STROBE G1/Rx2/RxCAN/SCL G9/SPI_EN/STROBE G7/Tx1/MISO GPS.TIMEPULSE G3/Tx0 G4/Rx0

G6/Rx1/MOSI G5/SCLK/STROBE G8/CS/STROBE G3/Tx0 G4/Rx0 G2/Tx2TxCAN/SDA/STROBE G1/Rx2/RxCAN/SCL

G6/Rx1/MOSI G2/Tx2TxCAN/SDA/STROBE G1/Rx2/RxCAN/SCL G7/Tx1/MISO

R3 S e r2 470 R4 470 | GPS_RESET_N

G13/DRDY/XSDA

SPI-EN GPS.TP

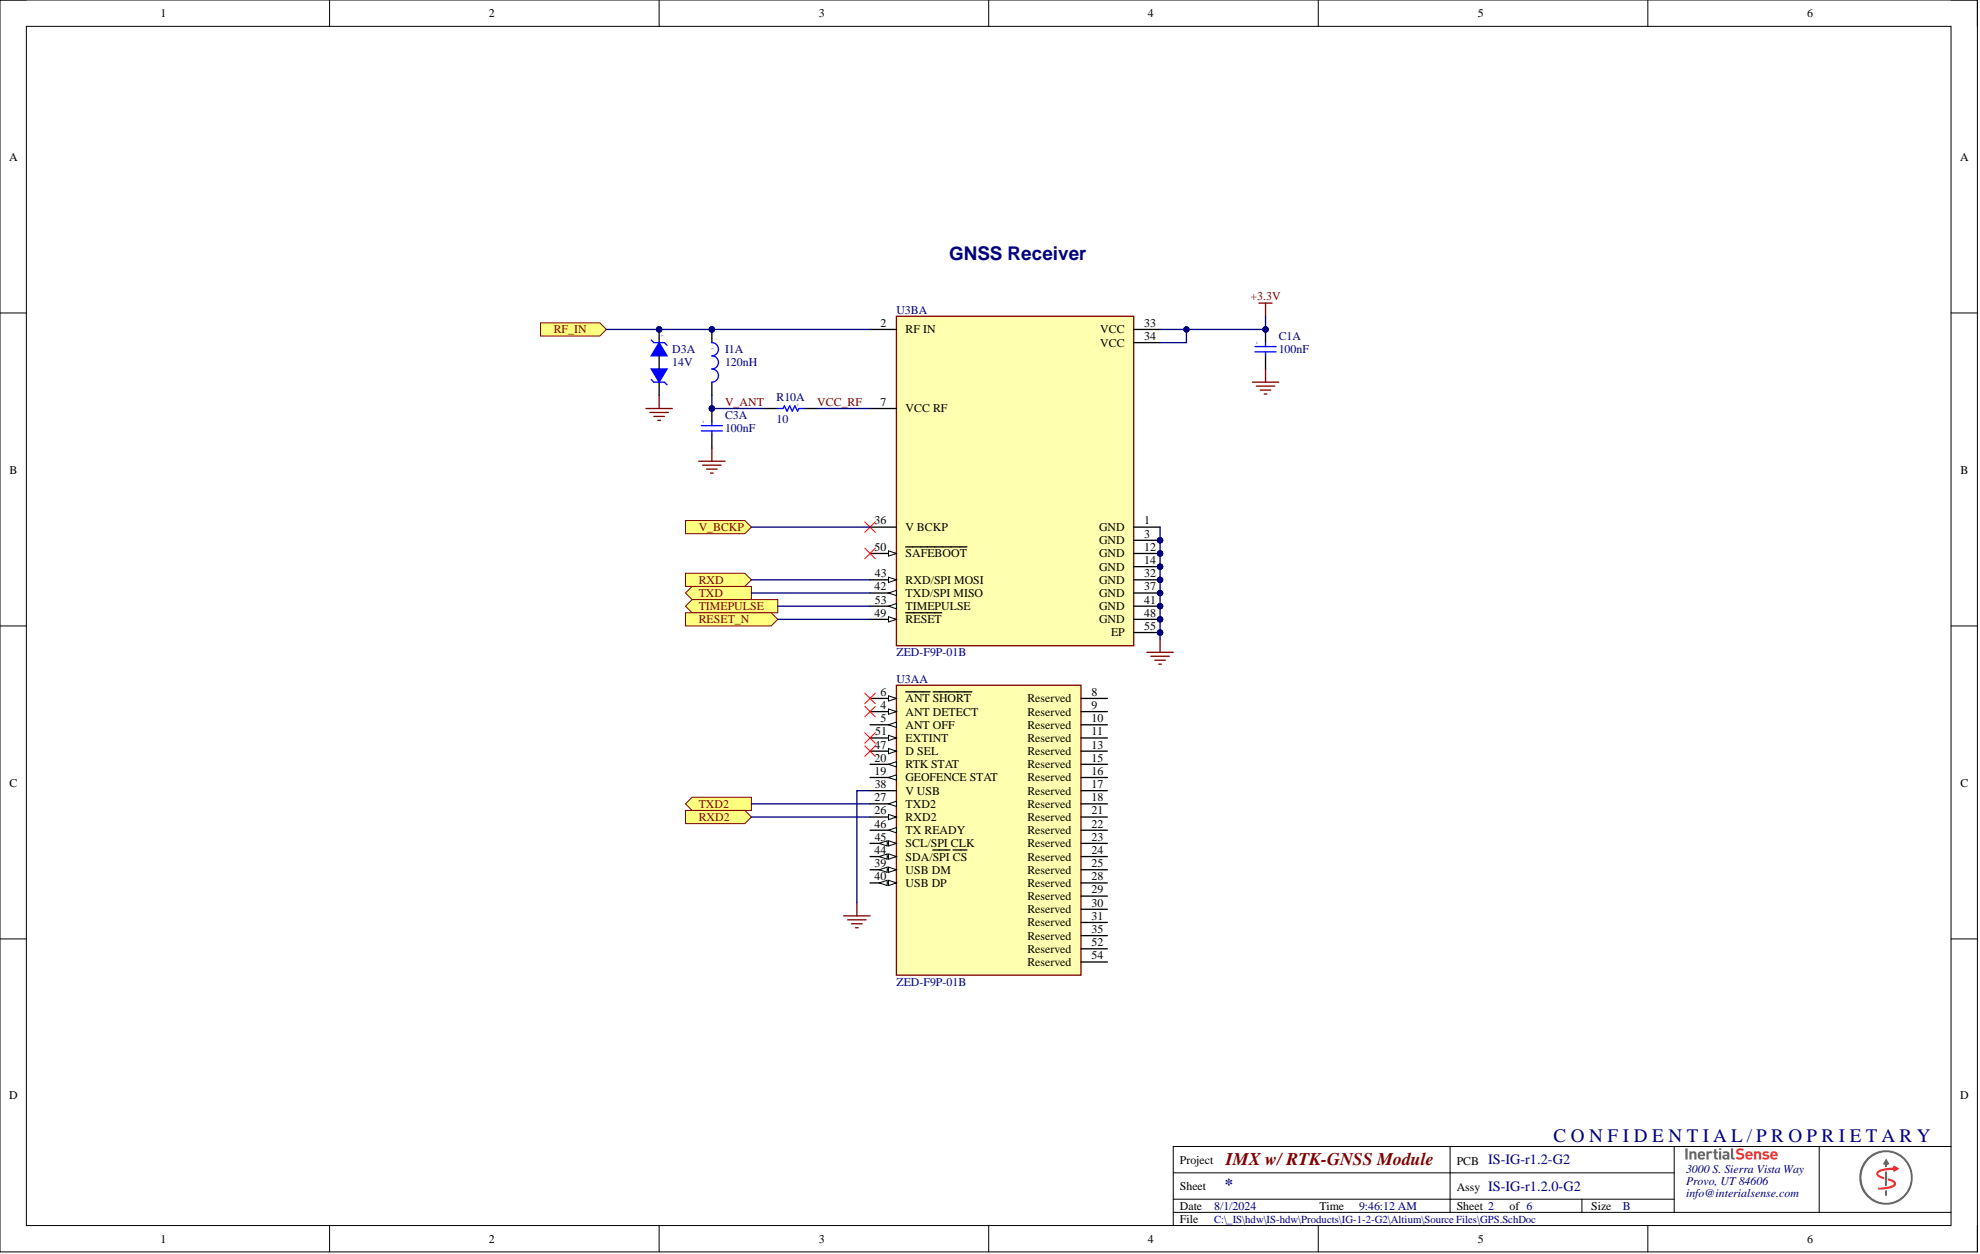
[picture p91: page 2]

C:\_IS\hdw\IS-hdw\Products\IG-1-2-G2\Altium\Source Files\GPS.SchDoc

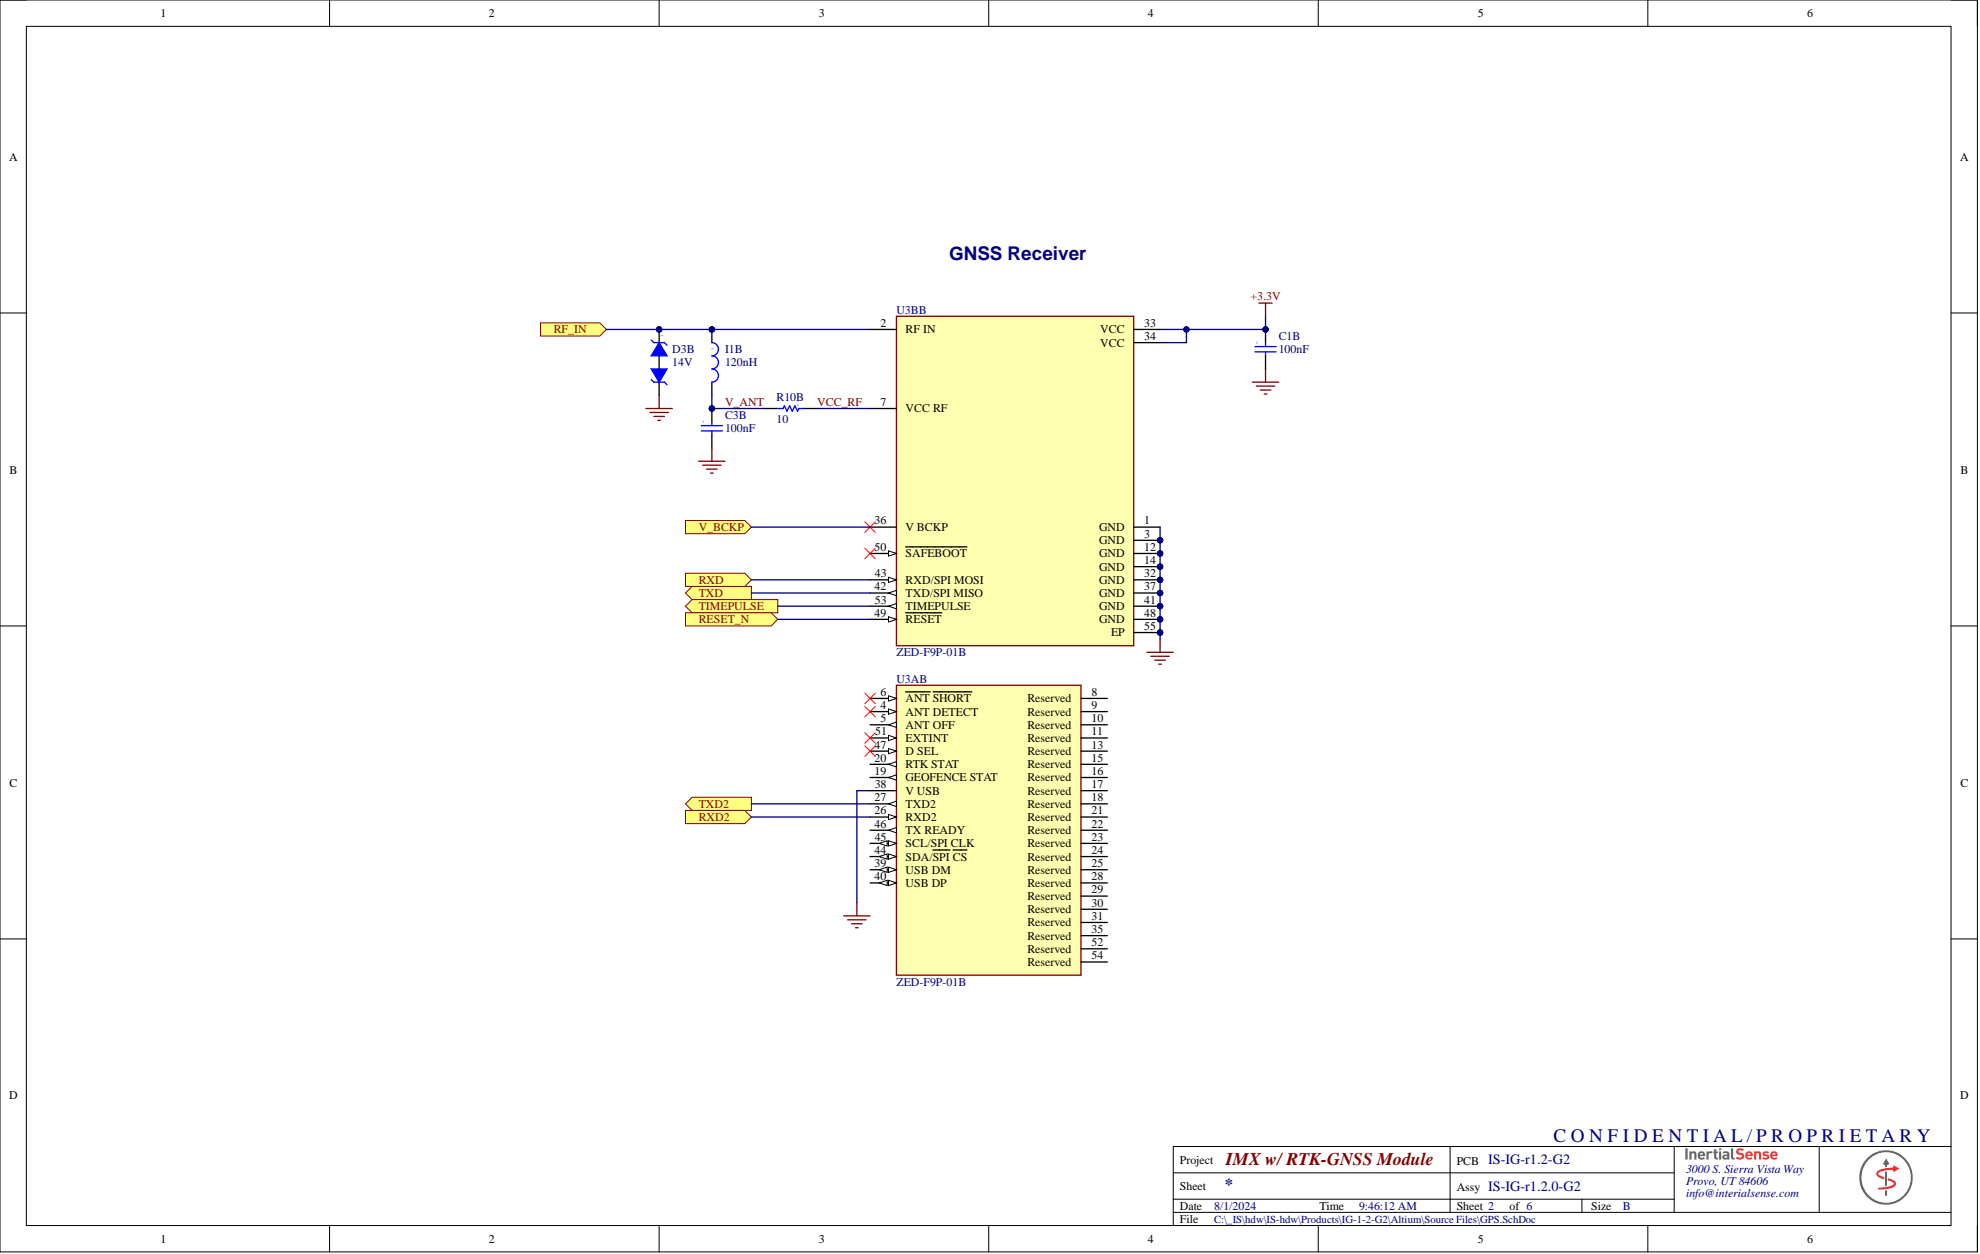
[picture p92: page 3]

C:\_IS\hdw\IS-hdw\Products\IG-1-2-G2\Altium\Source Files\GPS.SchDoc
