inertialsense/IS-hdw/Products/EVB-2/EVB-2-1/Images/PCB 3D Print - Bottom.PDF

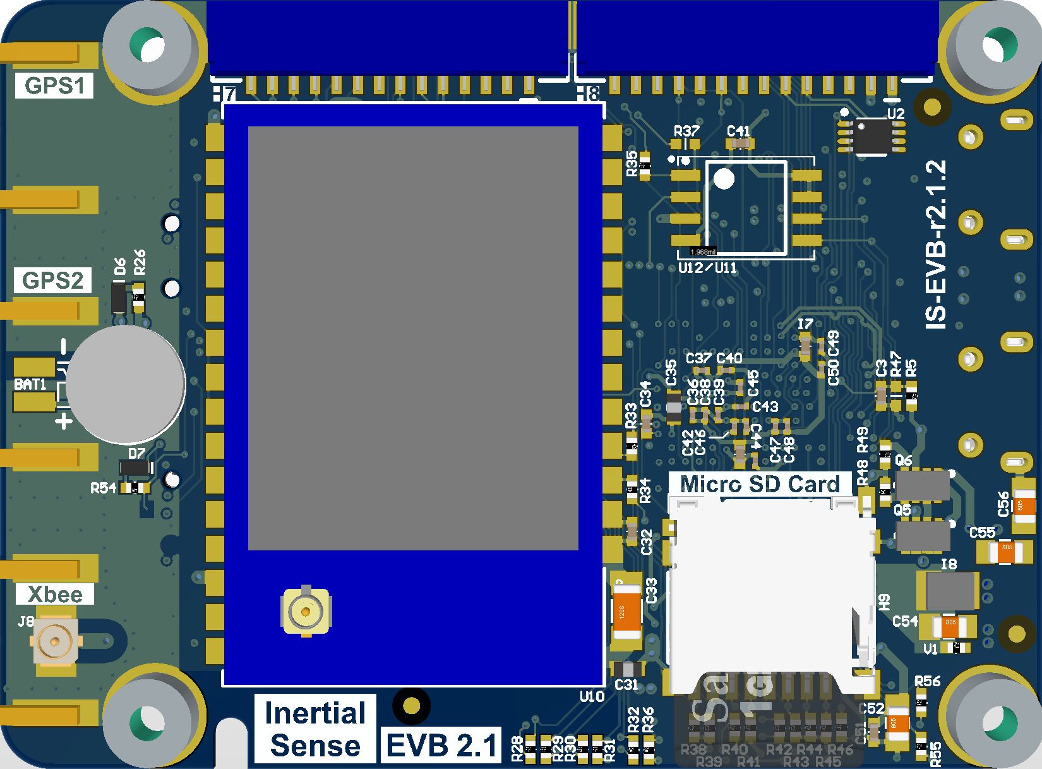
[picture p93: page 1]
