inertialsense/IS-hdw/Products/EVB-2/EVB-2-1/Images/PCB 3D Print - Top.PDF

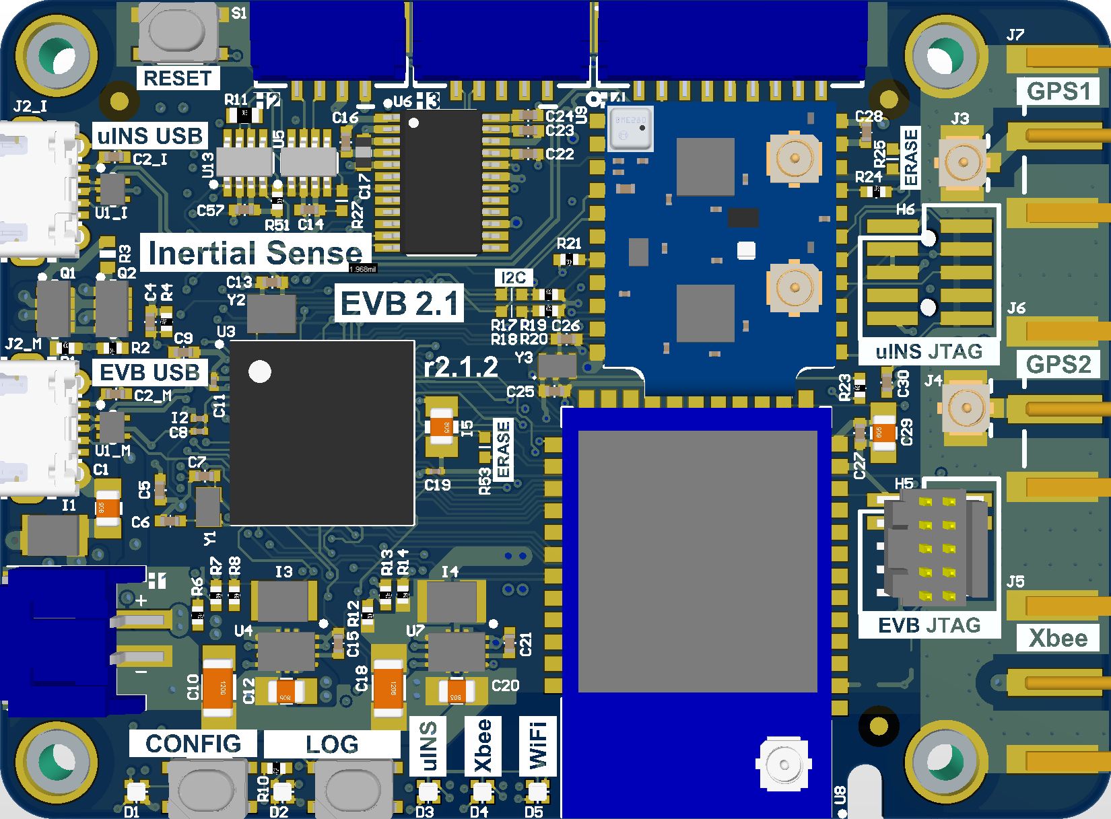
[picture p94: page 1]
