inertialsense/IS-hdw/Products/EVB-2/EVB-2-1/Images/PCB 3D Prints - Iso.PDF

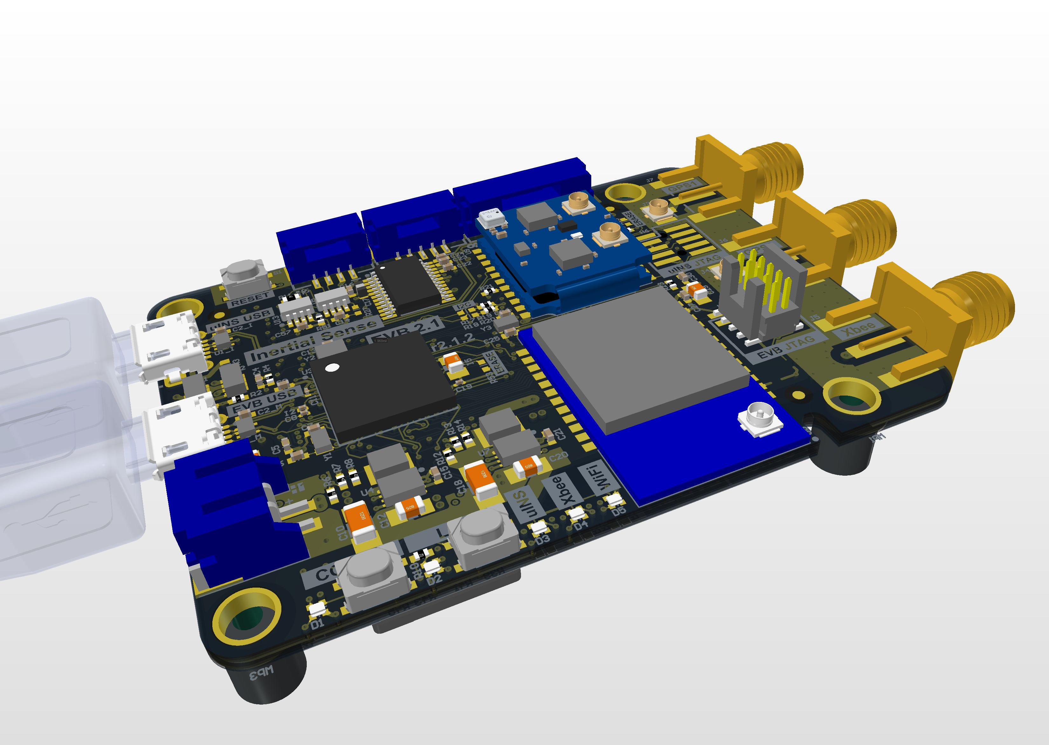
[picture p95: page 1]
