inertialsense/IS-hdw/Products/EVB-1/EVB-1-5/Images/PCB 3D Print - Bottom.PDF

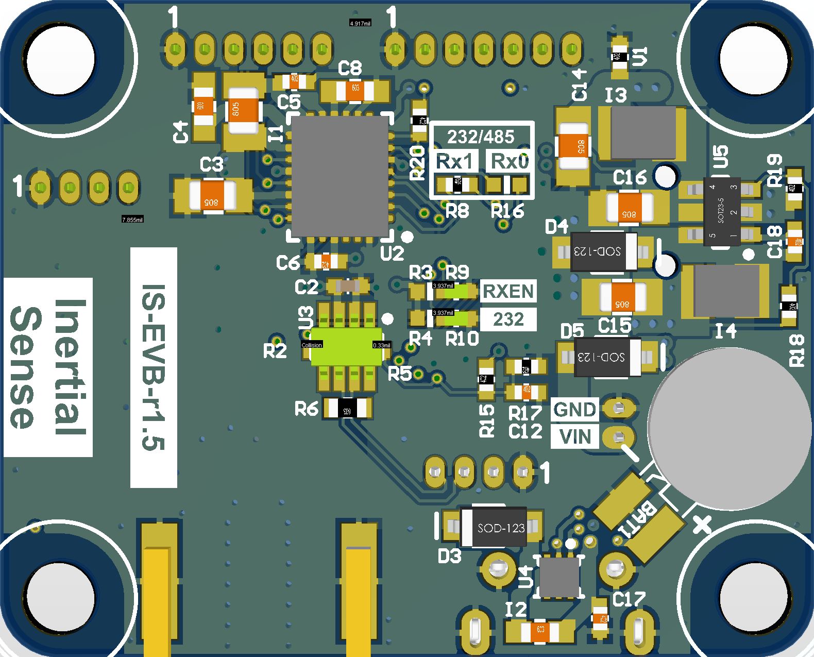
[picture p96: page 1]
