inertialsense/IS-hdw/Products/EVB-1/EVB-1-5/Images/PCB 3D Print - Top.PDF

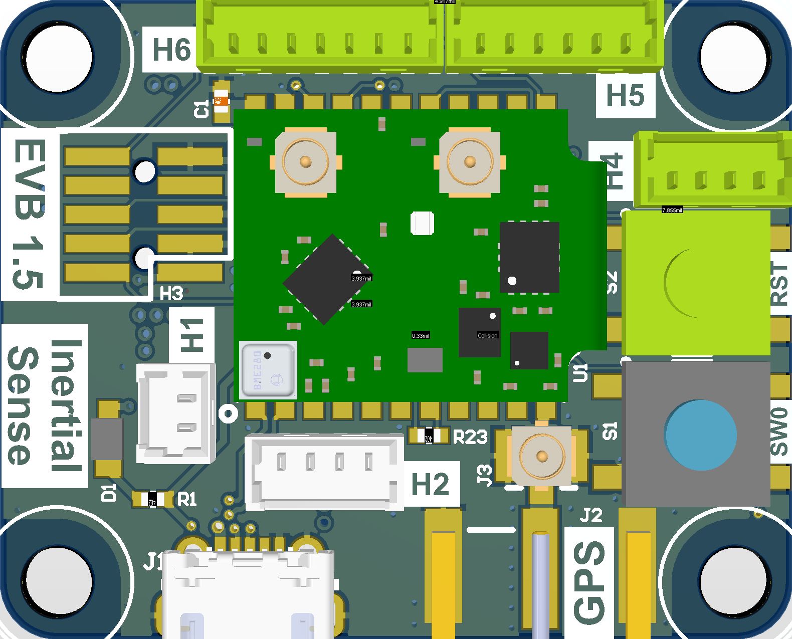
[picture p97: page 1]
