inertialsense/IS-hdw/Products/IG-3/IG-3-0-G/PCB_Library/IS-IG-2_footprint.pdf

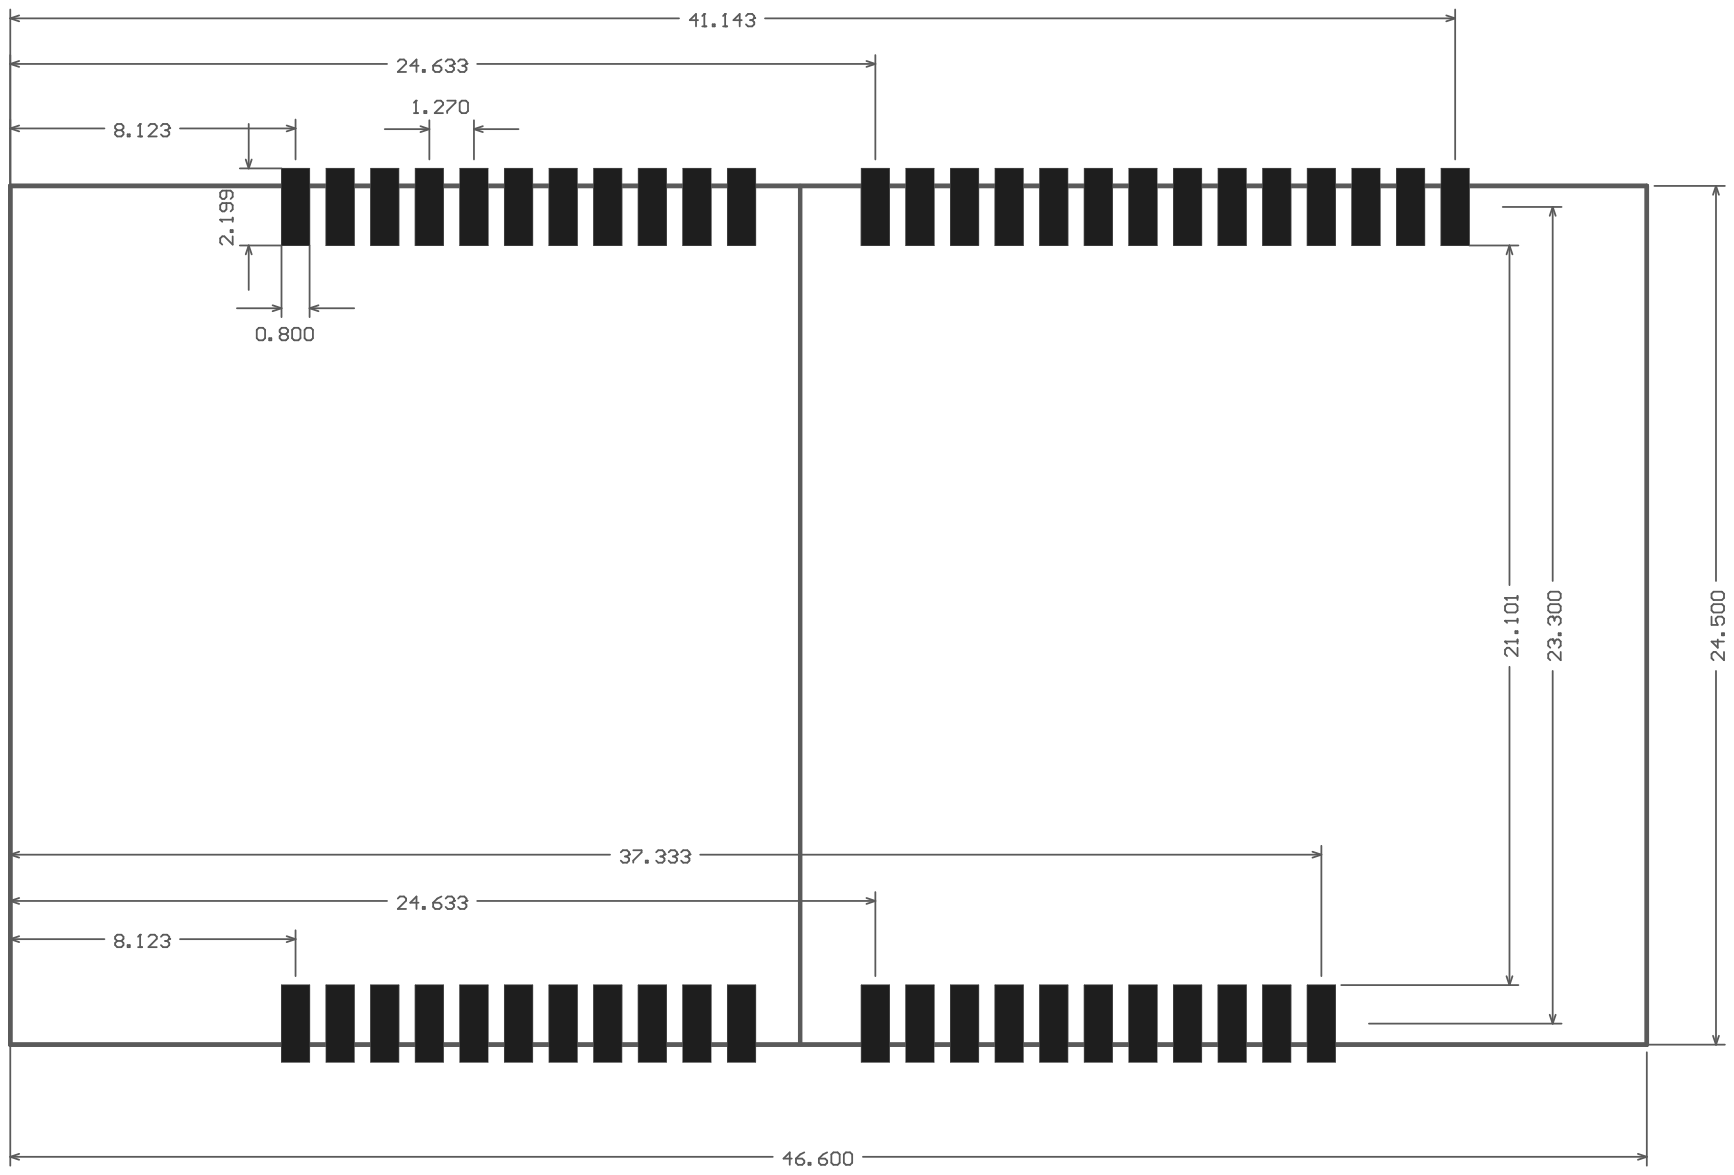
[picture p98: page 1]
